kwiecinski/BMS-and-offgrid-photovoltaic-management-system/docs/energy-meters/gama350_diode_dimensions1.jpg

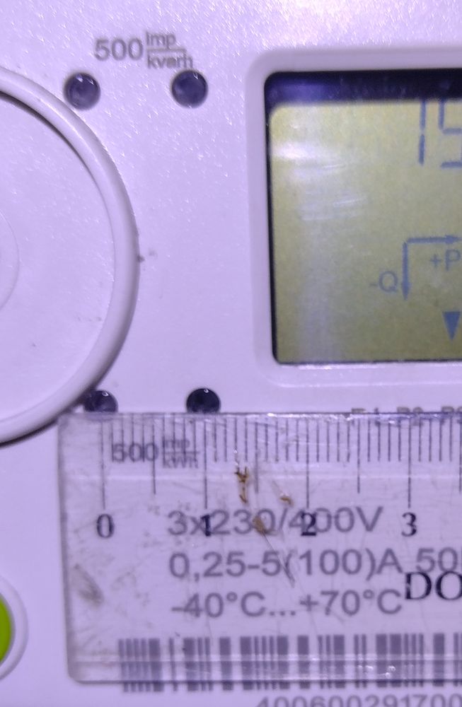
docs/energy-meters/gama350_diode_dimensions1.jpg
