kwiecinski/BMS-and-offgrid-photovoltaic-management-system/docs/FL-2C Shunt Resistor Dimensions.webp

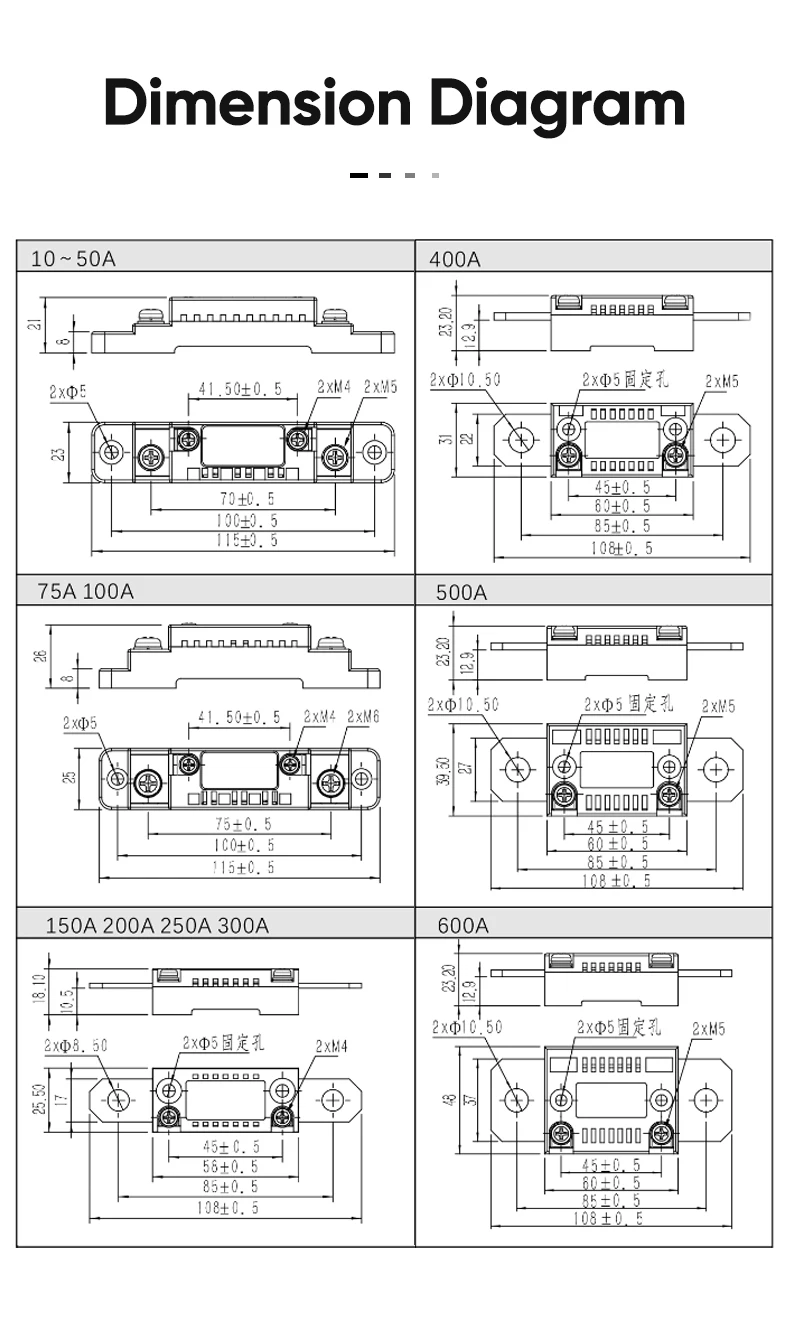
docs/FL-2C Shunt Resistor Dimensions.webp
