kwiecinski/BMS-and-offgrid-photovoltaic-management-system/docs/lt1492-voltage-controlled-current-sink.png

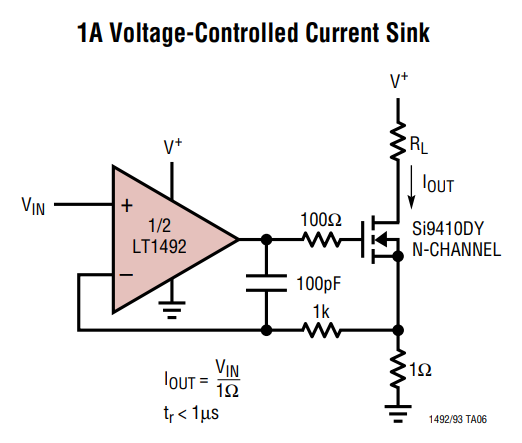
docs/lt1492-voltage-controlled-current-sink.png
