kwiecinski/BMS-and-offgrid-photovoltaic-management-system/docs/photos/ground-mount-structure/single_steel_post.jpg

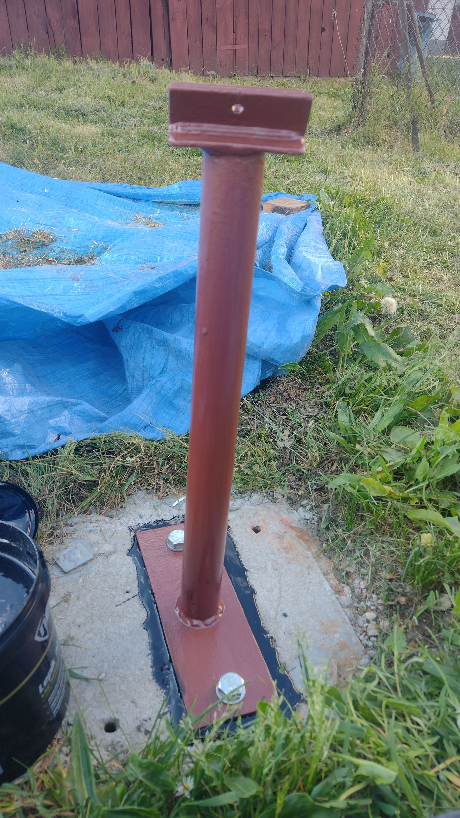
docs/photos/ground-mount-structure/single_steel_post.jpg
