kwiecinski/BMS-and-offgrid-photovoltaic-management-system/docs/photos/ground-mount-structure/steel-workshop-and-painting-09.jpg

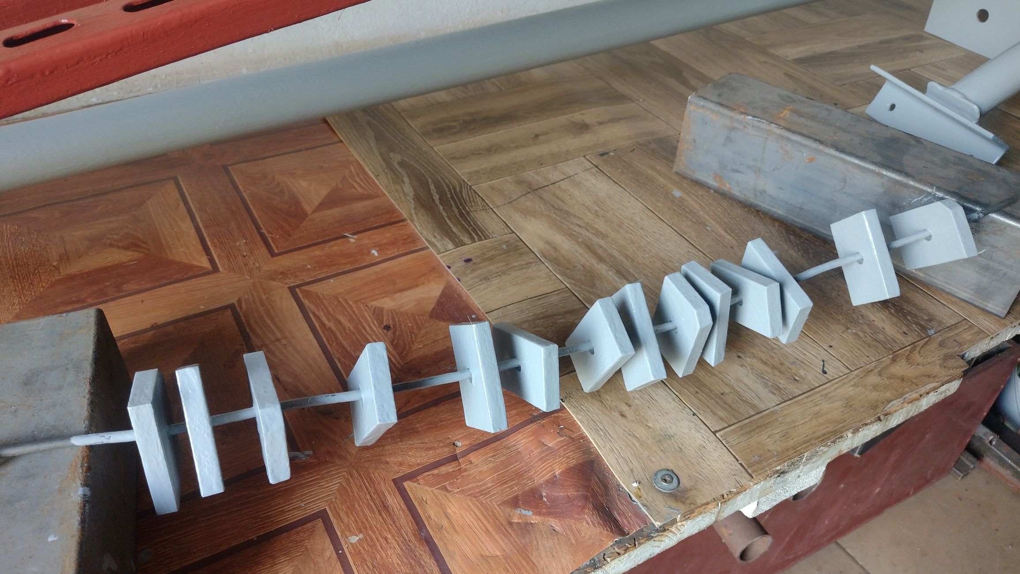
docs/photos/ground-mount-structure/steel-workshop-and-painting-09.jpg
