kwiecinski/BMS-and-offgrid-photovoltaic-management-system/docs/photos/shunt-resistor.jpg

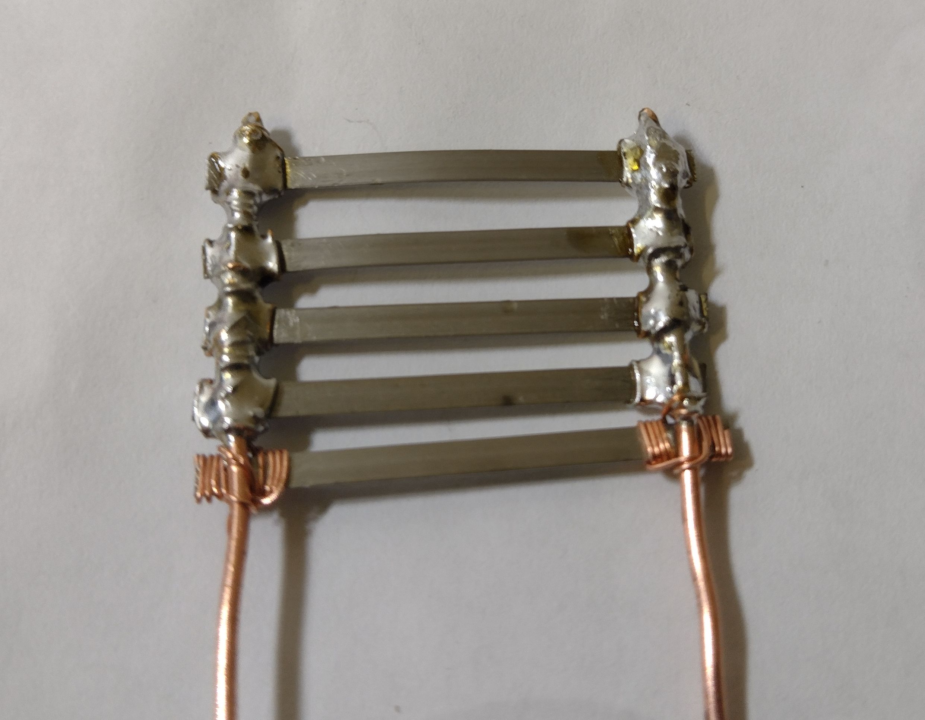
docs/photos/shunt-resistor.jpg
