kwiecinski/BMS-and-offgrid-photovoltaic-management-system/docs/xl4015/DC-DC-Buck-Converter.jpg

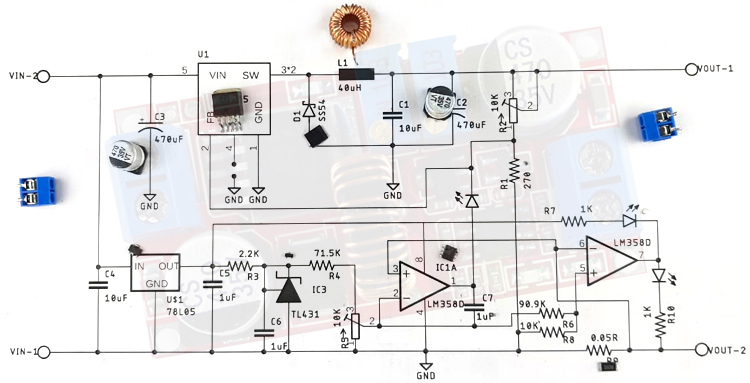
docs/xl4015/DC-DC-Buck-Converter.jpg
