kwiecinski/BMS-and-offgrid-photovoltaic-management-system/docs/zero crossing circuit.jpg

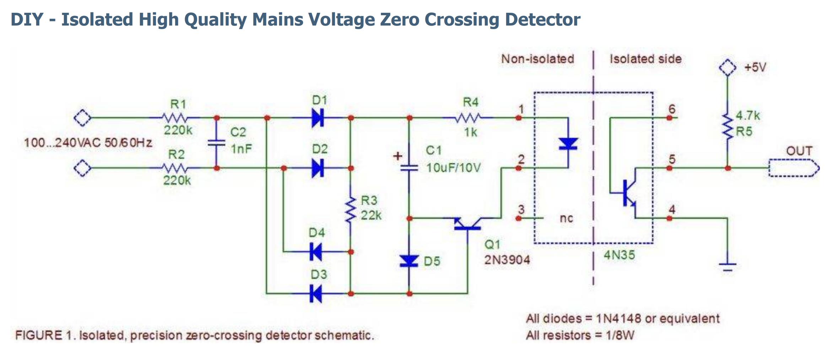
docs/zero crossing circuit.jpg
