kwiecinski/BMS-and-offgrid-photovoltaic-management-system/docs/connector/Phoenix contact SDDC 1,5 - 5-PV-3,5.pdf

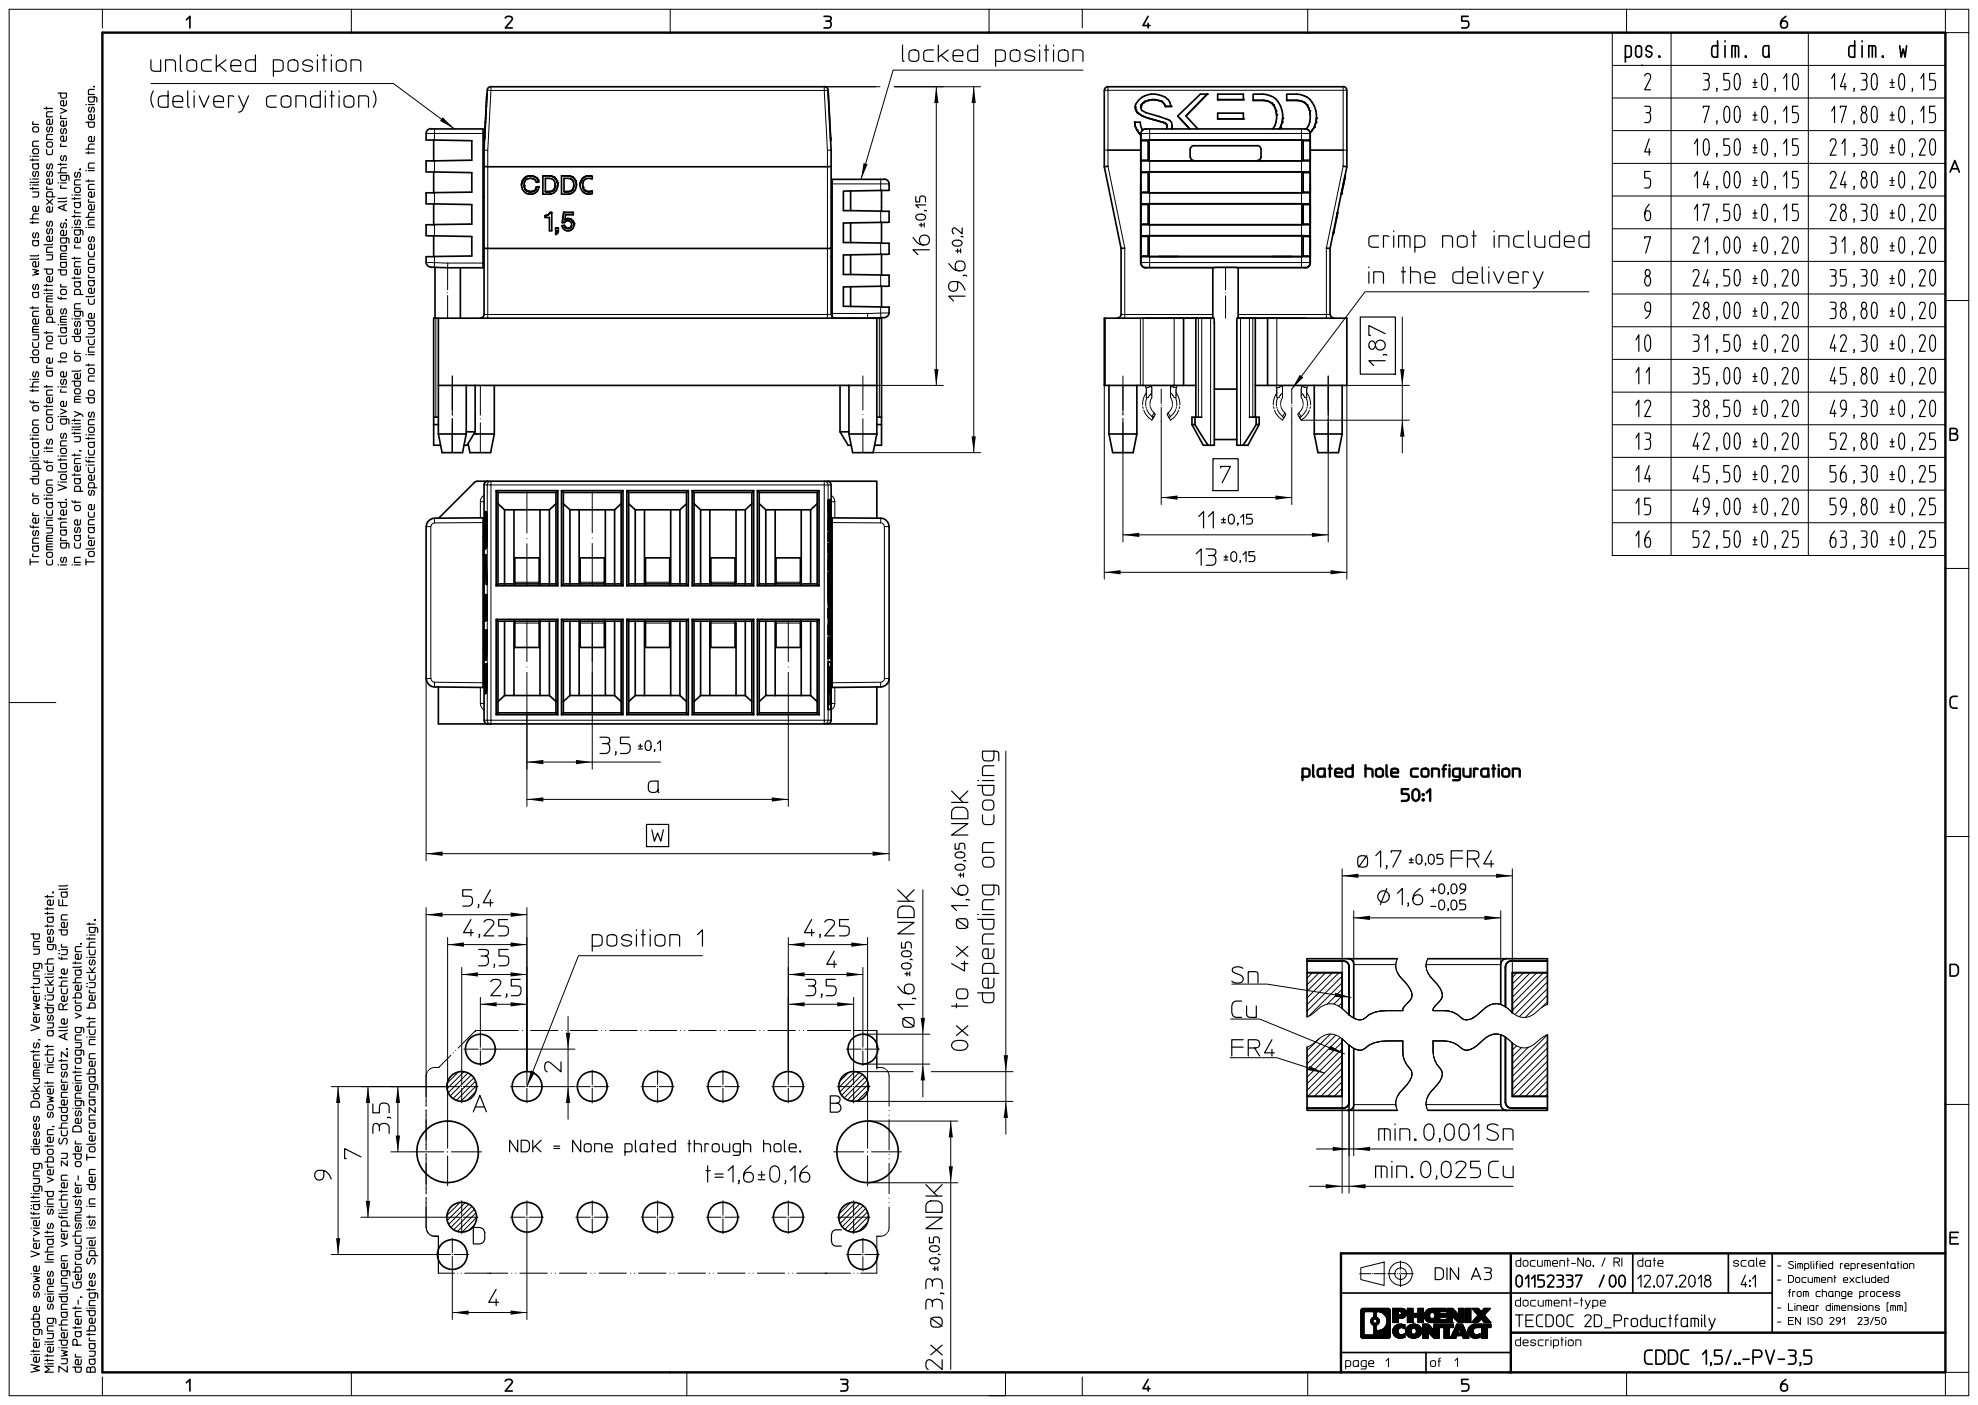
[picture p55: page 1]
