kwiecinski/BMS-and-offgrid-photovoltaic-management-system/simulation/analog_power_supply_op07.asc

C1: cap; 100p
C2: cap; 1000µ
C3: cap; 100p
D1: diode; 1N4148
D2: diode; 1N4148
Q1: npn; BC817-40
Q2: pnp; 2SA2094
Q3: pnp; D45H11
R1: res; 3k
R2: res; 10R
R3: res; 9k
R4: res; 1k
R5: res; 3k
R6: res; 1
R7: res; 1
R8: res; 10k
R9: res; 470
R11: res; 1k
U2: OP07
U3: OP07
V1: voltage; 12
V2: voltage; 5
V3: voltage; 5
V4: voltage; 50
V5: voltage; 5
V6: voltage; 5
Named nets: 0, -5V, +12v, +12V, +5V, Vout, base1
.tran 0 50m 100u
.include tl071.sub
