kwiecinski/BMS-and-offgrid-photovoltaic-management-system/simulation/analog_power_supply.asc

C1: cap; 1p
C2: cap; 100µ
C3: cap; 10n
D1: diode; 1N4148
D2: diode; 1N4148
D3: diode; 1N4148
D4: diode; 1N4148
Q1: pnp; BC807-25
Q2: npn; ZTX1048A
Q3: npn; ZTX1048A
Q4: npn; BC847A
R1: res; 100k
R2: res; 20R
R3: res; 9k
R4: res; 1k
R6: res; 1
R7: res; 1k
R8: res; 1
R9: res; 1k
R10: res; 1k
R12: res; 220R
U1: OP07
U2: OP07
V1: voltage; 12
V2: voltage; 5
V3: voltage; 5V
V4: voltage; 50
V5: voltage; 10
VREF: voltage; 2
Named nets: 0, -5V, +12v, Vout, +12V, +50V
.tran 0 50m 100n
.include tl071.sub
