kwiecinski/BMS-and-offgrid-photovoltaic-management-system/simulation/LTC4440.asc

C1: cap; 100n
C2: cap; 470µ
C3: cap; 1n
C4: cap; 10n
C5: cap; 100n
C6: cap; 10n
D1: schottky; 1N5819
D2: schottky; MBR745
D3: diode; 1N4148
D4: diode; 1N4148
D5: zener; BZX84C15L
L1: ind; 80µ
M1: nmos; BSC028N06LS3
R1: res; 10
R2: res; 10
R3: res; 100k
R4: res; 1k
U1: LTC4440
U2: NE555
V1: voltage; 12
V2: voltage; PULSE(0 5 0 1n 1n 1u 20u)
V3: voltage; 30
Named nets: 0, out, gate, source, neout
.tran 0 50m 0 1m
