kwiecinski/BMS-and-offgrid-photovoltaic-management-system/simulation/charge_pump_from_uc.asc

C1: cap; 10µ
C2: cap; 100µ
D1: diode; 1N4148
D2: diode; 1N4148
Q1: npn; BC817-25
Q2: npn; BC817-25
Q3: pnp; BC557C
R1: res; 10k
R2: res; 1k
R3: res; 200
V1: voltage; 5
V2: voltage; PULSE(0 5 1n 1n 1n 100u 200u)
Named nets: 0
.tran 0 100m 1m
