kwiecinski/BMS-and-offgrid-photovoltaic-management-system/simulation/gnd_diff.asc

R1: res; 10
R2: res; 1k
R3: res; 0.5
R4: res; 1Meg
R5: res; 0.5
R6: res; 0.1
R7: res; 10k
R8: res; 10k
R10: res; 10k
R11: res; 10k
R12: res; 1k
R13: res; 10k
R14: res; 10k
R15: res; 10k
R16: res; 10k
U1: ADTL082
U2: ADTL082
U3: ADTL082
V1: voltage; -5
V2: voltage; -10
V3: voltage; 12
V4: voltage; 30
V5: voltage; 2.5
V6: voltage; 500m
Named nets: 0, out, gnd_clean, vref, +12V, vbat
.tran 0 3m 0 200n
