kwiecinski/BMS-and-offgrid-photovoltaic-management-system/simulation/gnd_diff_opamp_tl082.asc

R1: res; 10
R2: res; 1k
R3: res; 0.5
R4: res; 1Meg
R5: res; 0.5
R6: res; 0.1
R7: res; 100k
R8: res; 10k
R9: res; 100k
R10: res; 100k
R11: res; 47k
R12: res; 47k
U1: ADTL082
U2: ADTL082
V1: voltage; -5
V2: voltage; -10
V3: voltage; 6.5
V4: voltage; 30
V5: voltage; 2.5
Named nets: 0, out, gnd_clean, +12V, vbat, vref
.tran 0 10m 0 100u
