kwiecinski/BMS-and-offgrid-photovoltaic-management-system/simulation/totem-pole driver low side.asc

M1: nmos; BSB015N04NX3
Q1: npn; BC337-40
Q2: pnp; BC327-40
Q3: npn; BC847B
R1: res; 10
R2: res; 5
R4: res; 5k
R5: res; 5k
R6: res; 220
V1: voltage; 10
V2: voltage; PULSE(0 5 1n 1n 1n 10u 50u)
V3: voltage; 10
Named nets: 0, pulse_source, out, gate
.tran 0 200u 0 10n startup
