kwiecinski/BMS-and-offgrid-photovoltaic-management-system/simulation/driver_chip.asc

M1: nmos; BSB015N04NX3
Q1: npn
R1: res; 1k
R2: res; 5
R4: res; 1k
U1: ADP3654
V1: voltage; 30
V2: voltage; PULSE(0 5 1n 1n 1n 1u 10u)
V3: voltage; 15
Named nets: 0, pulse_source, gate
.tran 0 80u 0 5n startup
