kwiecinski/BMS-and-offgrid-photovoltaic-management-system/simulation/totem-pole driver low side complementary.asc

C1: cap; 220p
M1: nmos; BSB015N04NX3
Q1: npn; BC337-40
Q2: pnp; BC327-40
Q3: npn; BC847B
Q4: pnp; BC327-40
Q5: pnp; BC327-40
Q6: npn; BC337-40
Q7: npn; BC847B
R1: res; 10
R2: res; 5
R3: res; 1k
R4: res; 470
R5: res; 10k
R6: res; 680
R7: res; 220
R8: res; 330
R9: res; 330
R10: res; 330
R11: res; 10k
R12: res; 470
R13: res; 470
V1: voltage; 12
V2: voltage; PULSE(0 5 1n 1n 1n 500n 40u)
Named nets: 0, pulse_source, out, gate
.tran 0 200u 0 10n startup
