kwiecinski/BMS-and-offgrid-photovoltaic-management-system/simulation/pnp_driver.asc

D2: schottky; 1N5819
Q1: pnp; 2SB1705
Q2: pnp; 2SB1705
Q3: npn; BC847B
R1: res; 1k
R2: res; 5
R3: res; 1k
R4: res; 4k7
V1: voltage; 28
V2: voltage; PULSE(0 5 1n 1n 1n 1u 50u)
V3: voltage; 14
Named nets: 0, pulse_source
.tran 0 200u 0 10n startup
