kwiecinski/BMS-and-offgrid-photovoltaic-management-system/simulation/totem-pole driver.asc

C1: cap; 10n
C2: cap; 10n
D1: schottky; BAT54
D2: schottky; 1N5819
M1: nmos; BSB015N04NX3
Q1: npn; BC337-40
Q2: pnp; BC327-40
Q3: npn; BC847B
R1: res; 100
R2: res; 5
R3: res; 0
R4: res; 4k7
R5: res; 1.5k
R7: res; 100
V1: voltage; 28
V2: voltage; PULSE(0 5 1n 1n 1n 5u 50u)
V3: voltage; 14
Named nets: 0, pulse_source, out, gate
.tran 0 200u 0 10n startup
