kwiecinski/BMS-and-offgrid-photovoltaic-management-system/simulation/tl494_buck.asc

C1: cap; 2.2n
C2: cap; 2000µ
C3: cap; 100n
D1: diode; 1N4148
D2: schottky; RB215T-90NZ
D3: diode; 1N4148
L1: ind; 38µ
M1: nmos; IRF7468
Q1: npn; BC337-40
Q2: pnp; BC327-40
Q3: npn; BC337-40
R1: res; 1K; tol=1 pwr=0.1
R2: res; 100; tol=1 pwr=0.1
R3: res; 5k
R4: res; 1k
R5: res; 10
R6: res; 300m
R7: res; 6.8k
R8: res; 4.7k
R9: res; 10k
R10: res; 51k
R11: res; 510
R12: res; 10k
R13: res; 100
R14: res; 1K; tol=1 pwr=0.1
U2: TL494
V1: voltage; 27
Named nets: 0, out, emiter_drive, gate
.tran 0 5m 0 1m uic
