kwiecinski/BMS-and-offgrid-photovoltaic-management-system/simulation/high_side_current_sense.asc

Q1: npn; BC817-40
R1: res; 6
R2: res; 10m
R3: res; 1k
R4: res; 100R
R5: res; 1k
R6: res; 10R
U2: ADTL082
V1: voltage; 28
V2: voltage; 31
Named nets: 0, diff_out
.tran 0 50m 0 5u
