kwiecinski/BMS-and-offgrid-photovoltaic-management-system/simulation/diff_opamp.asc

C1: cap; 10µ
C2: cap; 47µ
C4: cap; 47µ
D1: diode; 1N4148
D2: diode; 1N4148
D4: diode; 1N4148
D5: zener; UDZV30B
D6: diode; 1N4148
L1: ind; 47µ
M1: nmos
Q1: npn; BC547C
Q2: npn; BC547C
Q3: pnp; BC557C
Q4: npn; BC547C
Q5: pnp; BC557C
Q6: npn; BC547C
Q7: npn; BC547C
R1: res; 100; tol=5
R2: res; 102; tol=5
R3: res; 100
R4: res; 1k
R5: res; 0.1
R6: res; 10
R7: res; 1k
R9: res; 1k
R10: res; 10k
R11: res; 1k
U1: ADTL082
V1: voltage; 32
V2: voltage; 29
V4: voltage; PULSE(0 5 0 0 0 50u 100u)
V5: voltage; 5
Named nets: 0, out, vopamp, -V
.tran 0 25m 0 200n
