kwiecinski/BMS-and-offgrid-photovoltaic-management-system/simulation/fan_reg.asc

C1: cap; 1µ
C2: cap; 470µ
Q1: npn; 2SC5866
R1: res; 2k2
R2: res; 100k
R3: res; 1k
R4: res; 10k
R5: res; 6.2k
R6: res; 24
U1: LM358
V1: voltage; 13.8
V2: voltage; PULSE(0 5 1n 1n 1n  {Tperiod-Ton} {Tperiod})
V3: voltage; 28
Named nets: 0, out, base, pwm_filtered
.tran 0 15m 0 500n
.param duty=0
.param freq=10k
.param Tperiod={1/freq}
.param Ton={Tperiod*duty}
