kwiecinski/BMS-and-offgrid-photovoltaic-management-system/simulation/fan_smps.asc

C1: cap; 470µ
C2: cap; 22n
D1: schottky; RBR30NS40A
D2: diode; 1N4148
D3: diode; 1N4148
L1: ind; 35µ
M1: nmos; IRFH5406
Q1: npn; BC337-40
Q2: pnp; BC327-40
Q3: npn; BC847B
R1: res; 5R
R2: res; 100R
R3: res; 4k7
R4: res; 4k7
V1: voltage; 28
V2: voltage; PULSE(0 5 1n 1n 1n 5u 10u)
V3: voltage; -12
Named nets: 0, OUT, pulse_source, gate, source
.tran 0 5m 0 50n startup
