kwiecinski/BMS-and-offgrid-photovoltaic-management-system/electrical/PV_electrical.kicad_sch

## KiCad design electrical/PV_electrical.kicad_sch (2025-04-28)

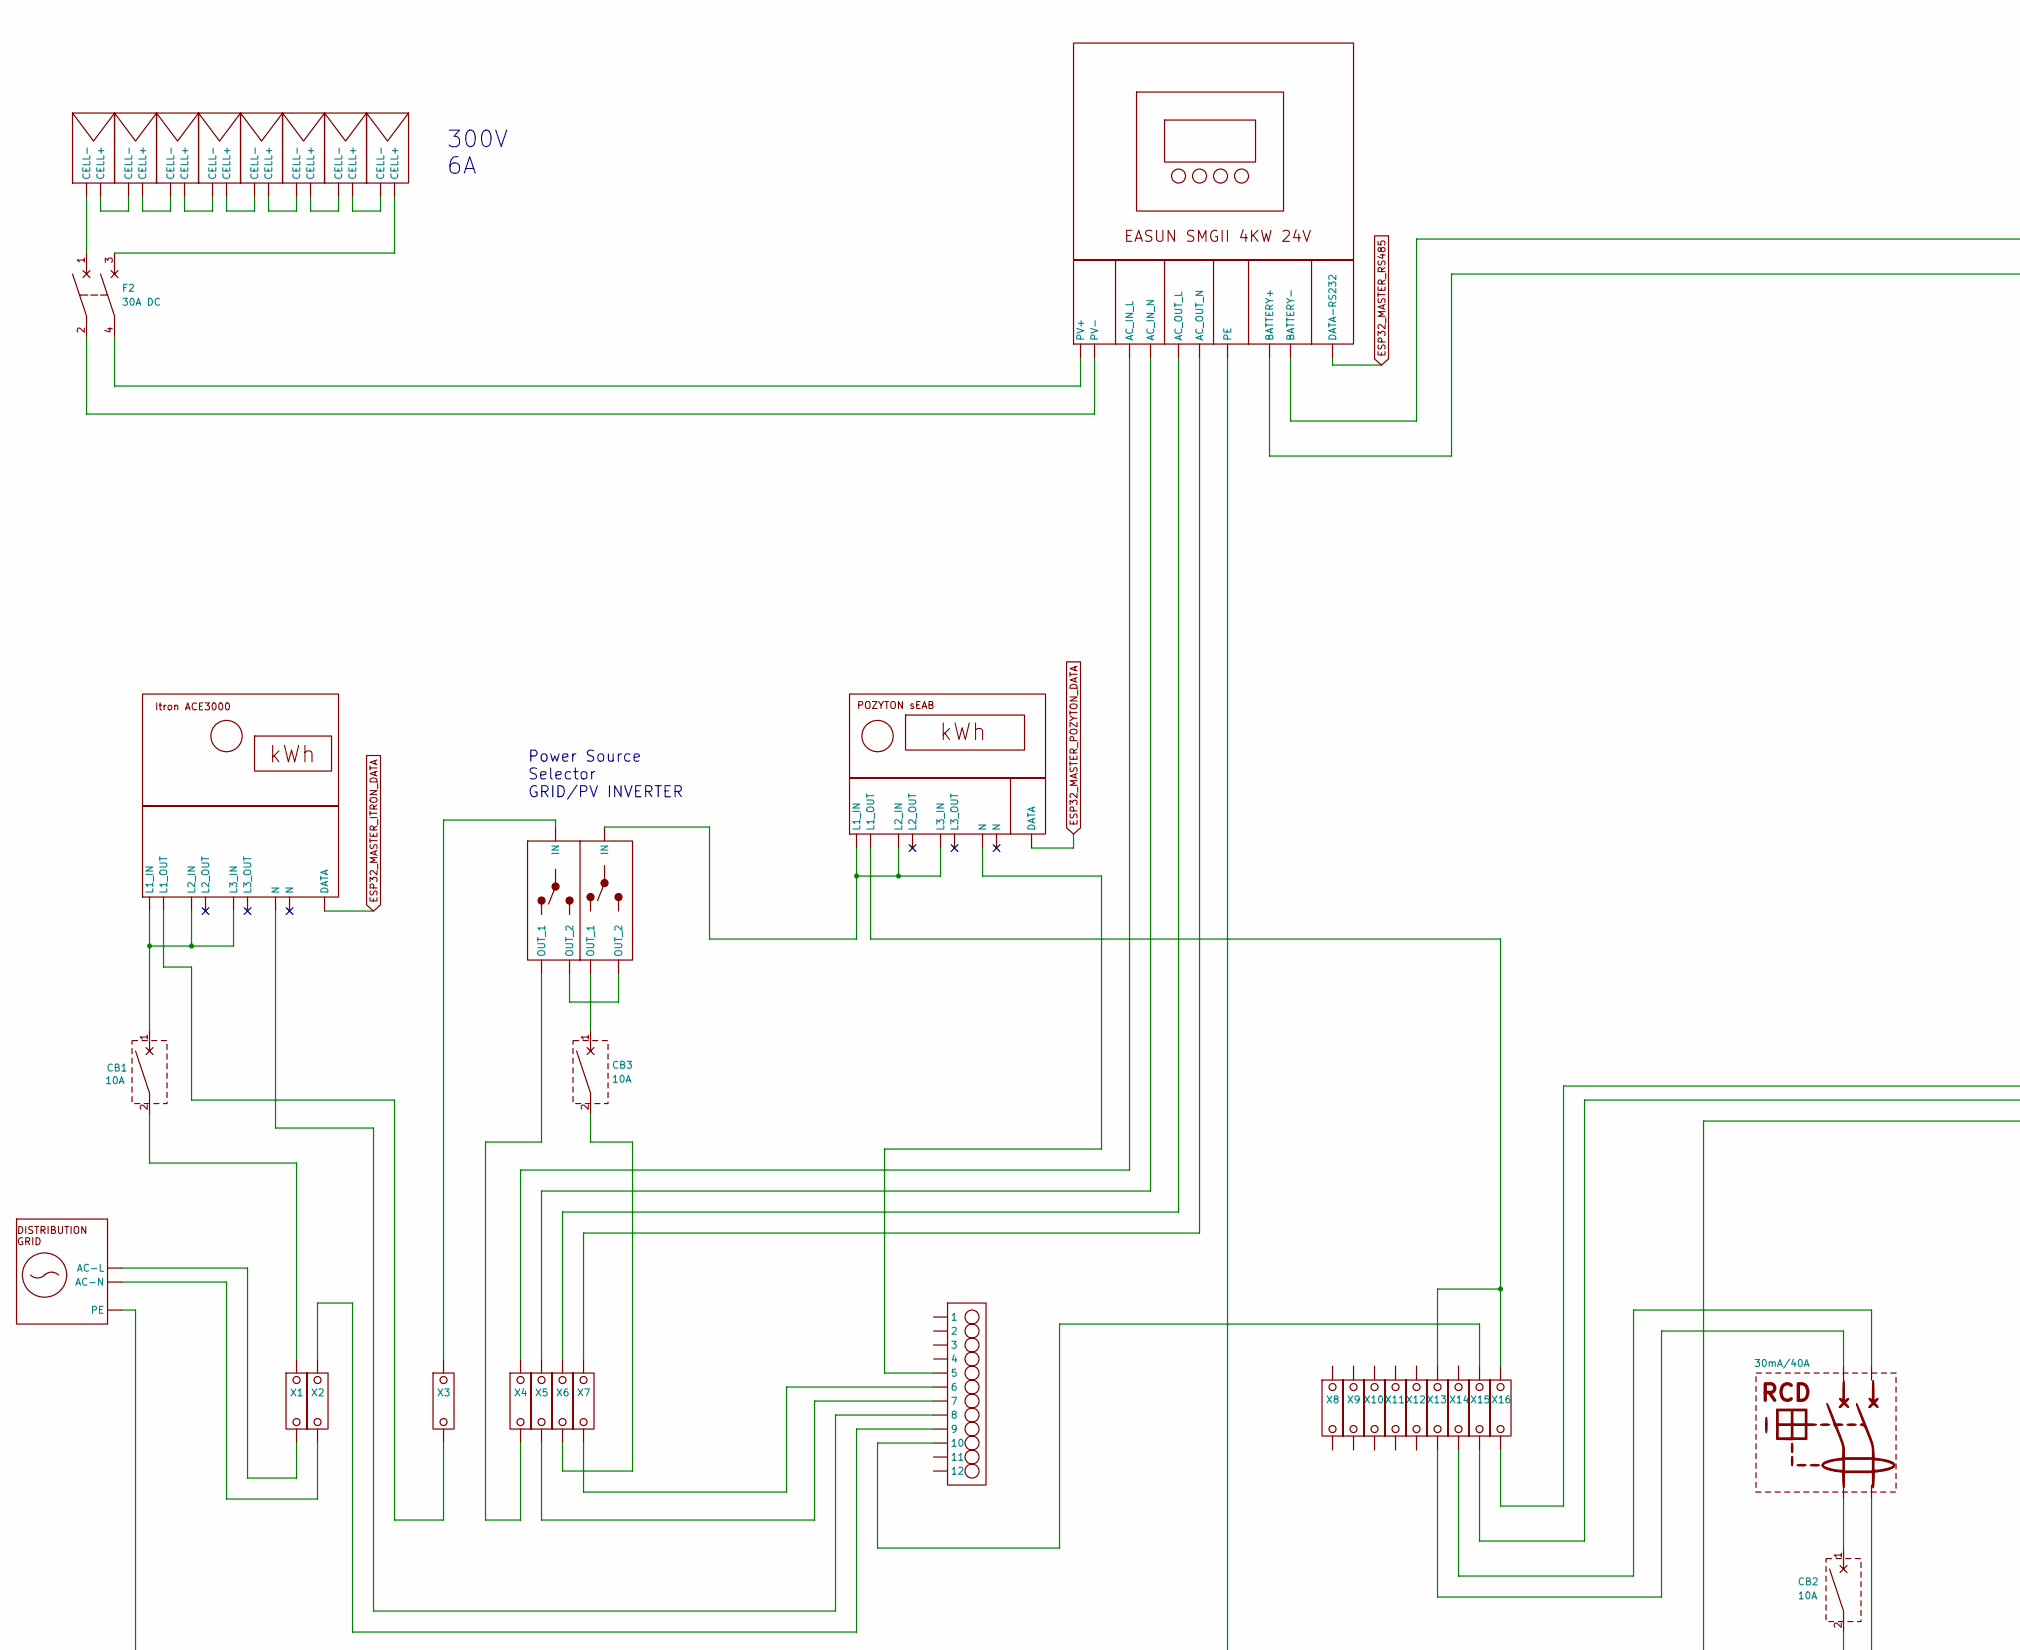
[picture p103: schematic PV_electrical.kicad_sch, part in row 1, column 1]

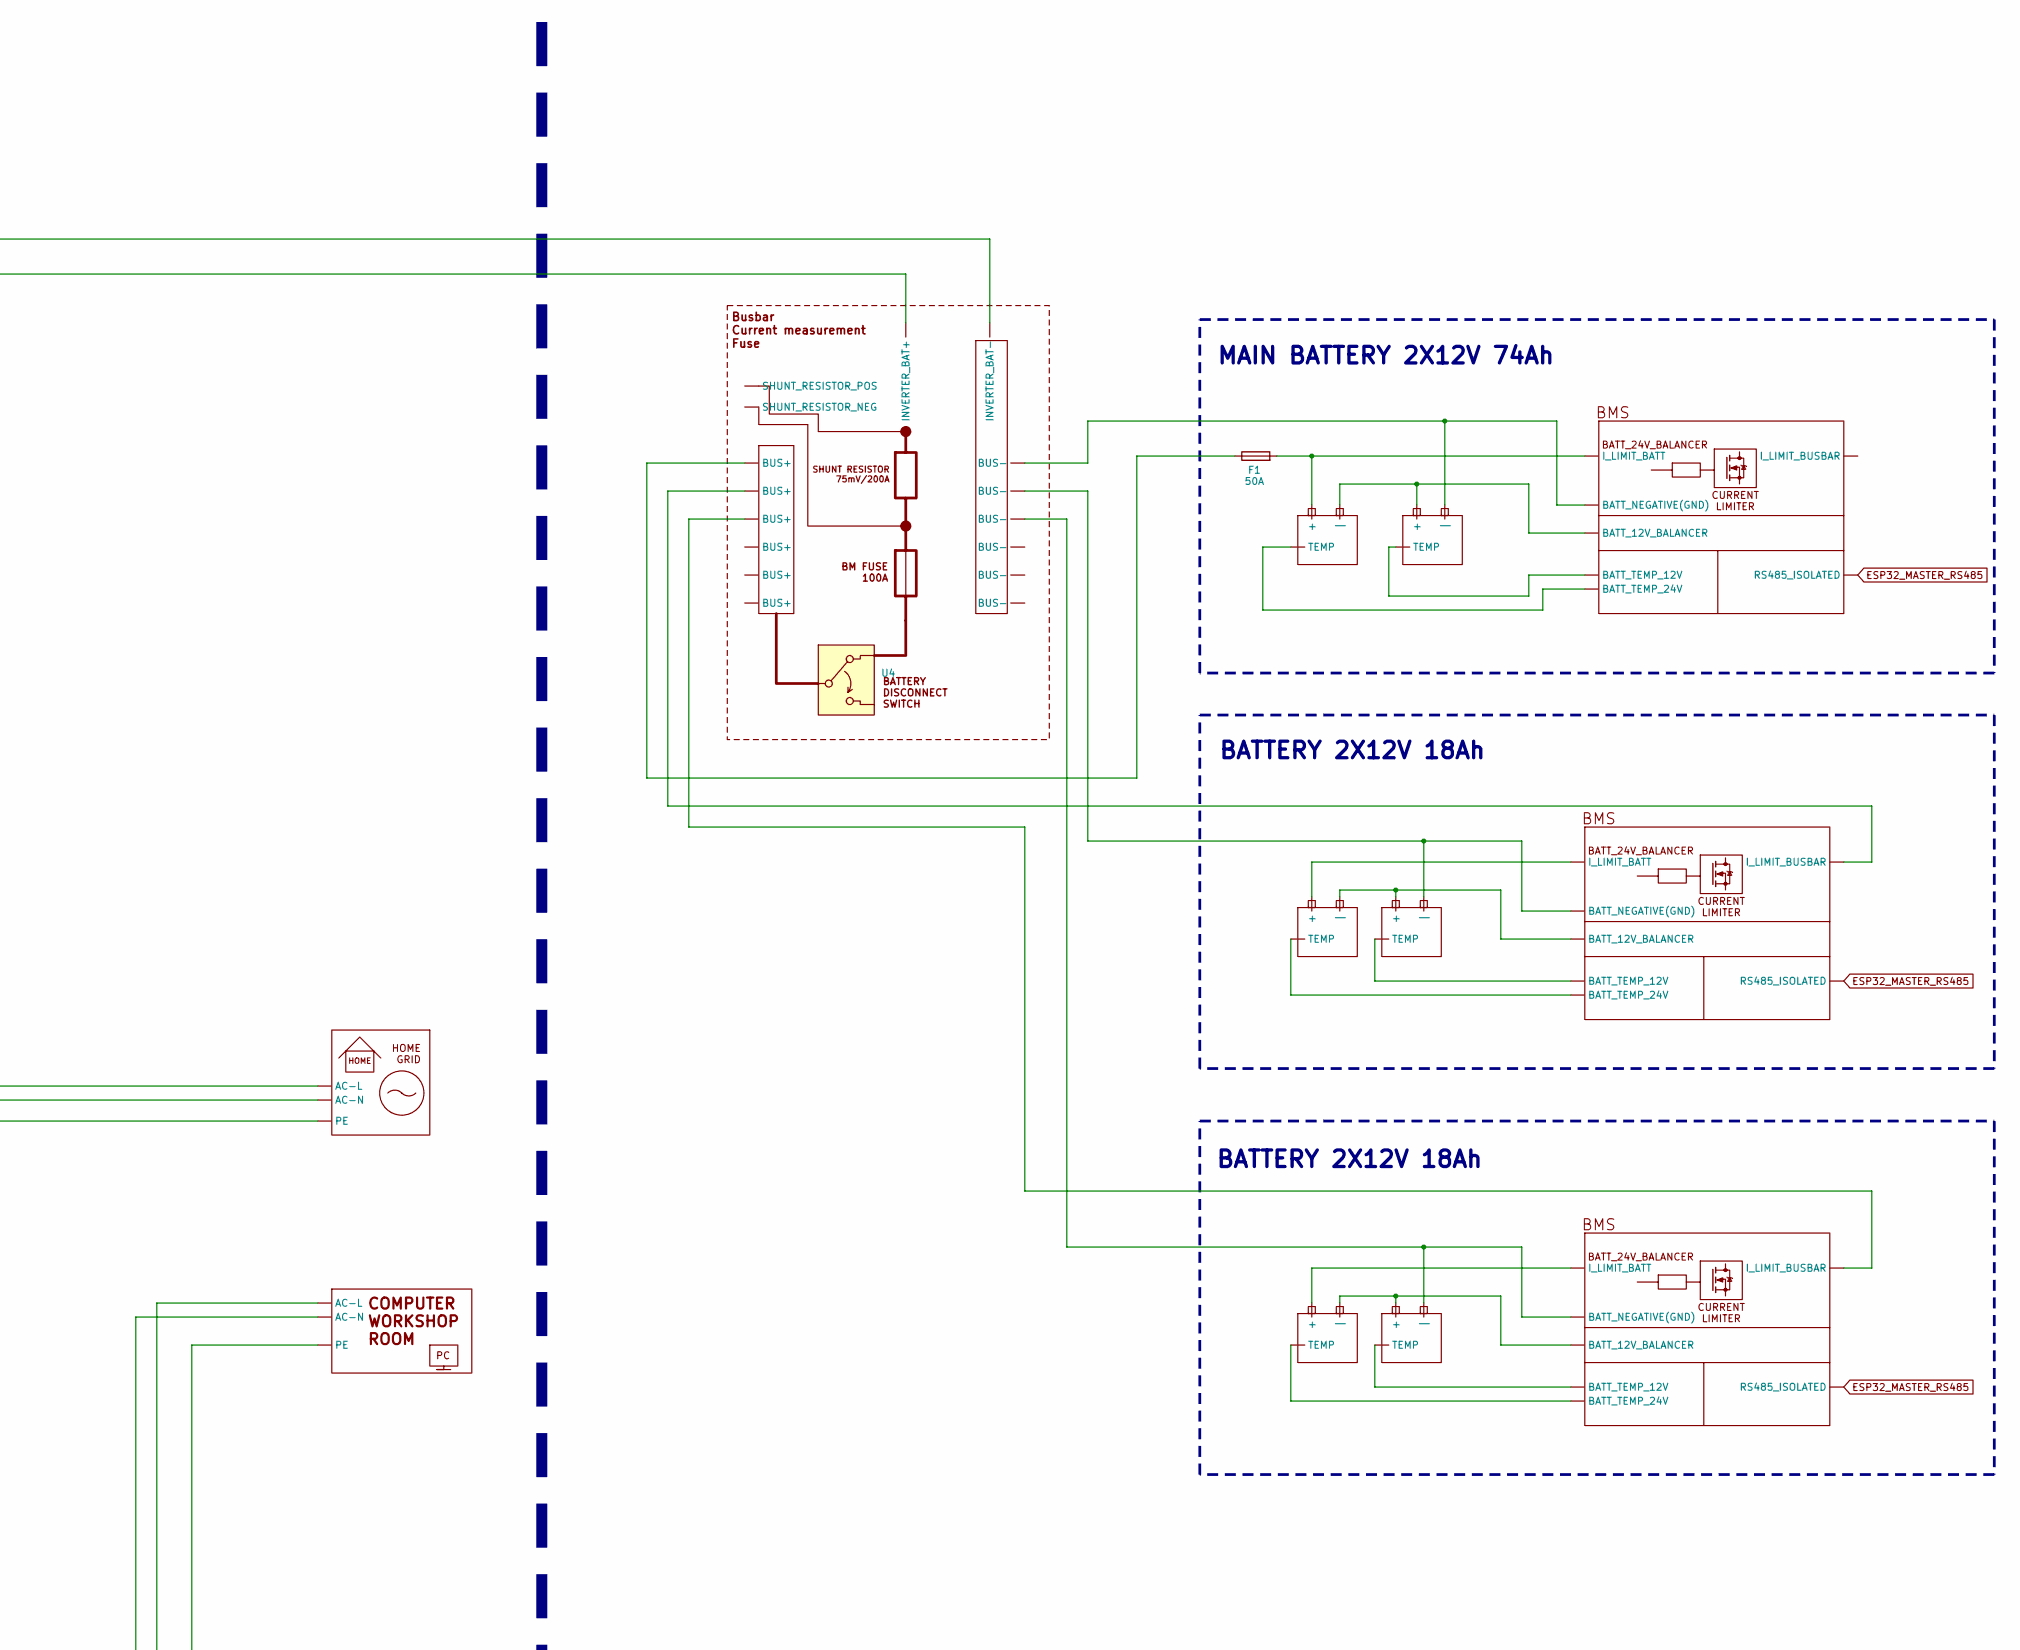
[picture p104: schematic PV_electrical.kicad_sch, part in row 1, column 2]

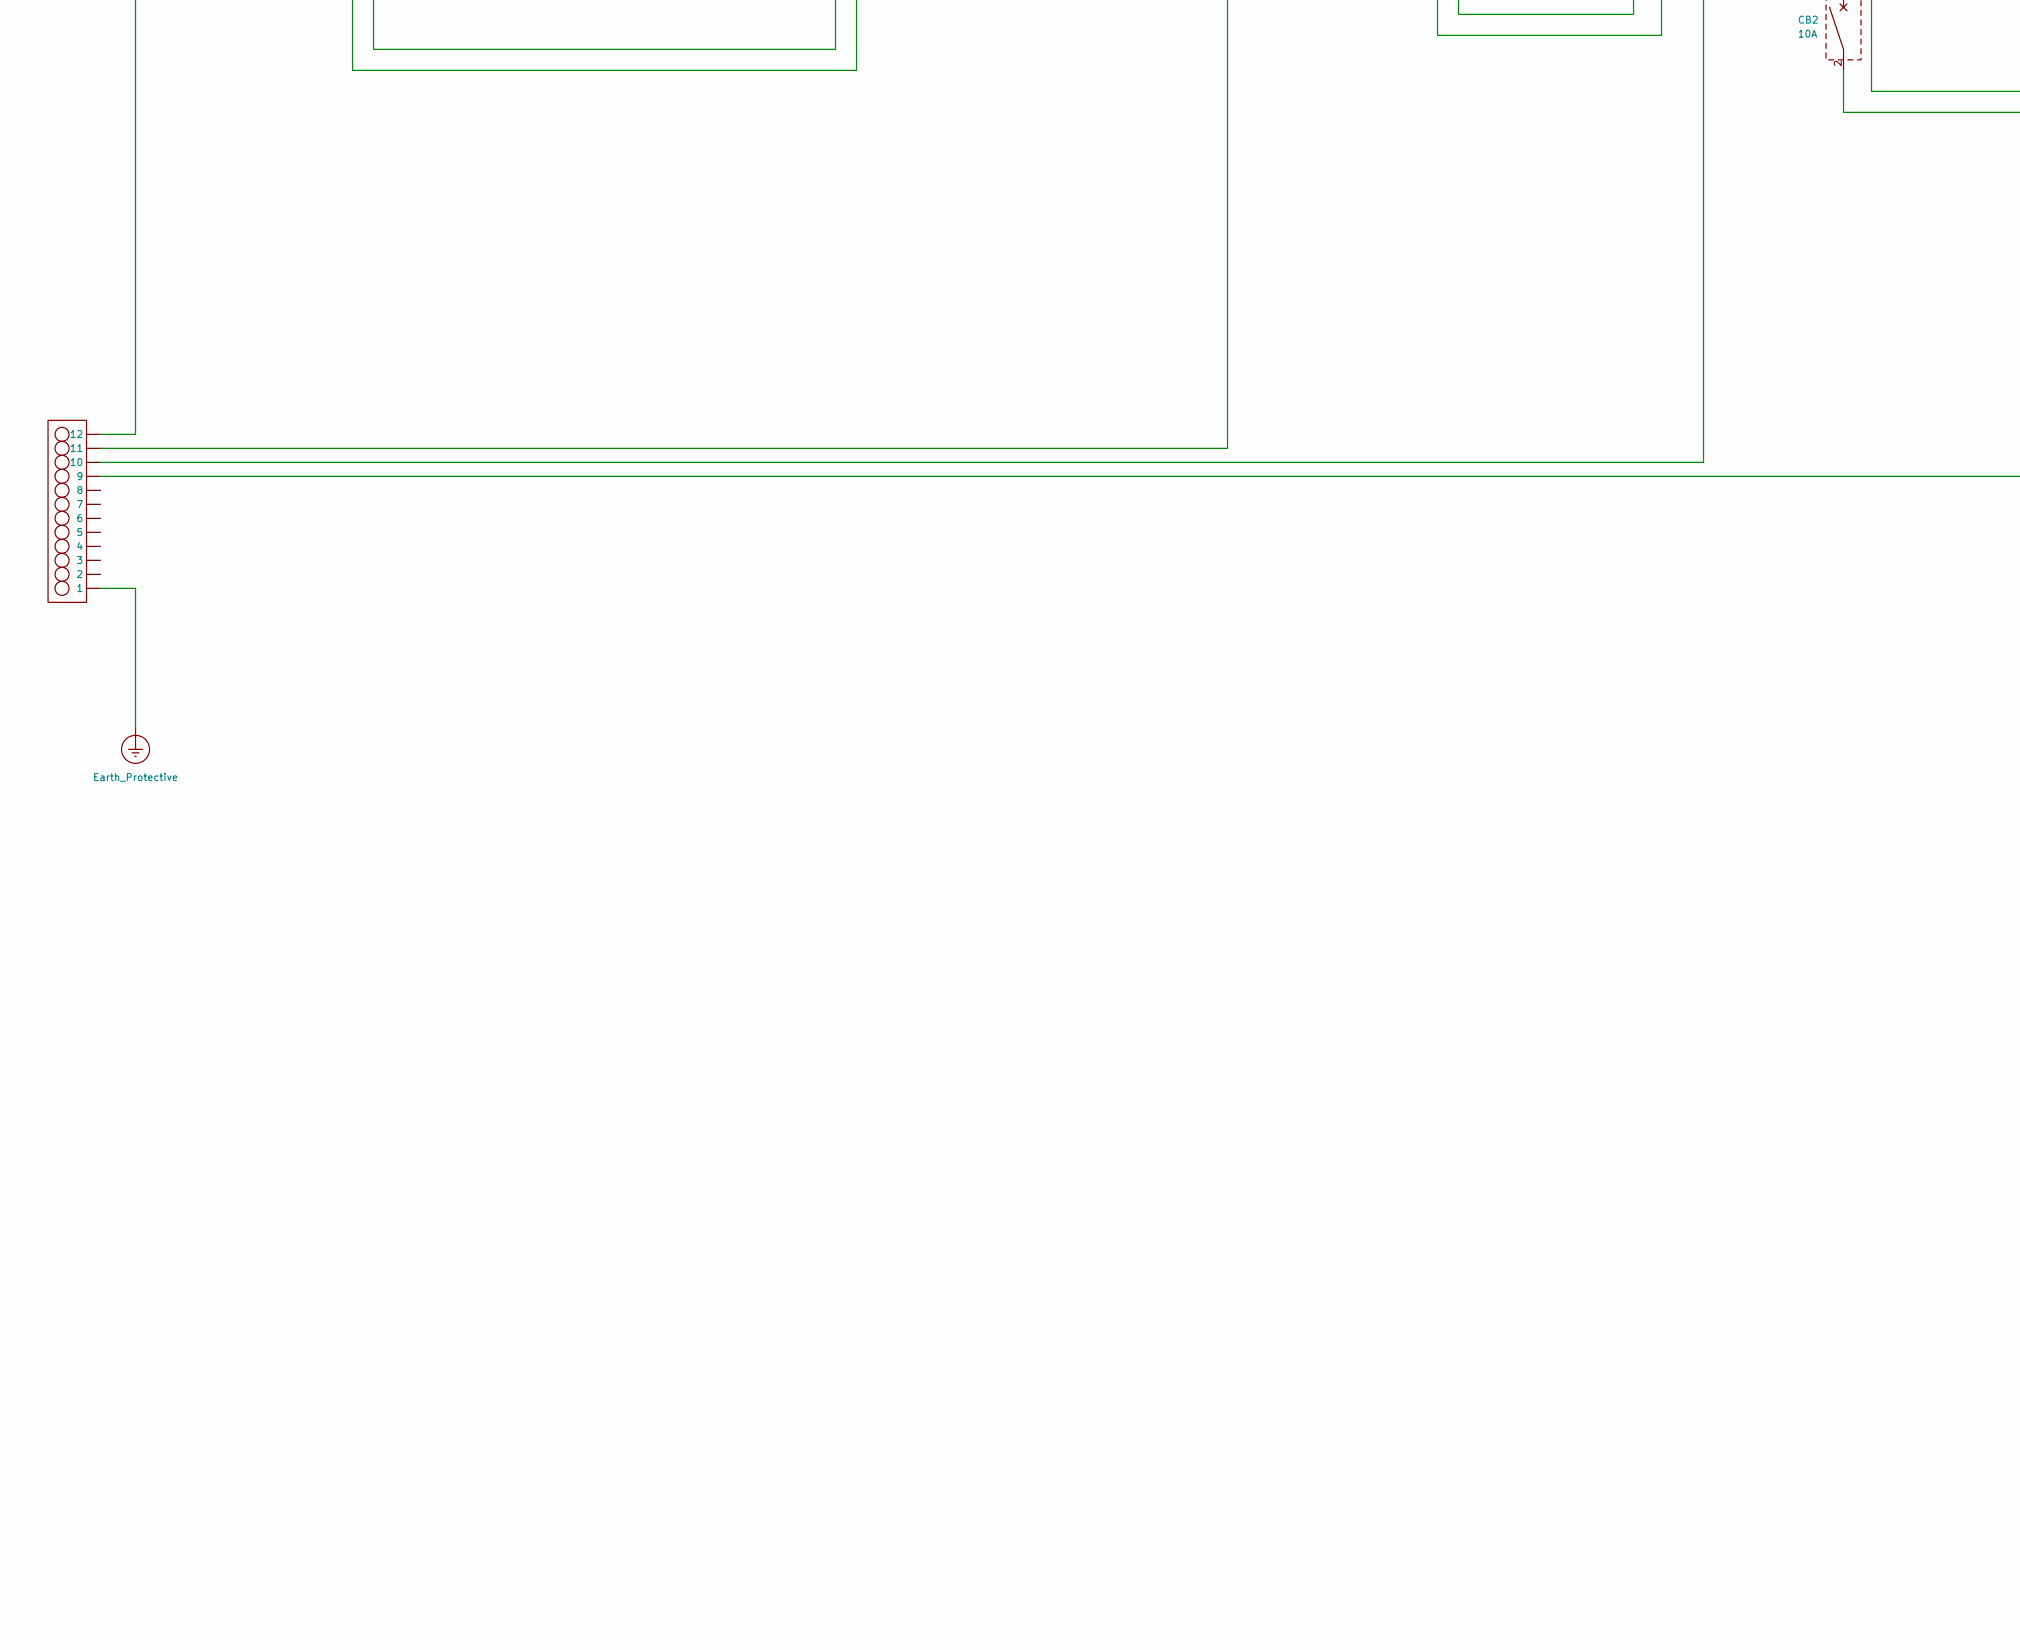
[picture p105: schematic PV_electrical.kicad_sch, part in row 2, column 1]

Parts:
B1, B2, B3, B4, B5, B6, B7, B8: (no value)
BAT1, BAT2, BAT3, BAT4, BAT5, BAT6: (no value)
BMS1, BMS2, BMS3: (no value)
CB1, CB2, CB3: 10A
D1: (no value)
F1: 50A
F2: 30A DC
F3: 30mA/40A
J1, J2: (no value)
M1: Itron ACE3000
M2: Pozyton-sEAB
SW1: (no value)
U1, U2, U3, U4: (no value)
X1, X2, X3, X4, X5, X6, X7, X8, X9, X10, X11, X12, X13, X14, X15, X16: (no value)

Connections:
ESP32_MASTER_ITRON_DATA: M1.
ESP32_MASTER_POZYTON_DATA: M2.
ESP32_MASTER_RS485: BMS1., BMS2., BMS3., U2.
Earth_Protective: J1.
unnamed: B1., B2., F2.1
unnamed: B2., B3.
unnamed: B3., B4.
unnamed: B4., B5.
unnamed: B5., B6.
unnamed: B6., B7.
unnamed: B7., B8.
unnamed: B8., F2.3
unnamed: BAT1., BAT2., BMS1., F1.2
unnamed: BAT2., BMS1., U4.
unnamed: BAT3., BAT4., BMS2.
unnamed: BAT4., BMS2., U4.
unnamed: BAT5., BAT6., BMS3.
unnamed: BAT6., BMS3., U4.
unnamed: BMS2., U4.
unnamed: BMS3., U4.
unnamed: CB1.1, M1.
unnamed: CB1.2, X1.
unnamed: CB2.1, F3.
unnamed: CB2.2, D1.
unnamed: CB3.1, SW1.
unnamed: CB3.2, X6.
unnamed: D1., F3., J1.
unnamed: F1.1, U4.
unnamed: F2.2, U2.
unnamed: F2.4, U2.
unnamed: F3., X13., X14.
unnamed: J1., U1., U2., U3.
unnamed: J2., M1., M2., X2., X5., X7., X15.
unnamed: M1., X3.
unnamed: M2., SW1., X13., X16.
unnamed: SW1., X3., X4.
unnamed: U1., X1., X2.
unnamed: U2., U4., X4., X5., X6., X7.
unnamed: U3., X15., X16.

Notes on the sheet:
Power Source Selector GRID/PV INVERTER
BATTERY 2X12V 18Ah
MAIN BATTERY 2X12V 74Ah
300V 6A
