kwiecinski/BMS-and-offgrid-photovoltaic-management-system/hardware/PCB_and_schematic/MPPT_controller/ESP_32_energy_meters_probe.kicad_sch

## KiCad design hardware/PCB_and_schematic/MPPT_controller/ESP_32_energy_meters_probe.kicad_sch (2024-09-15)

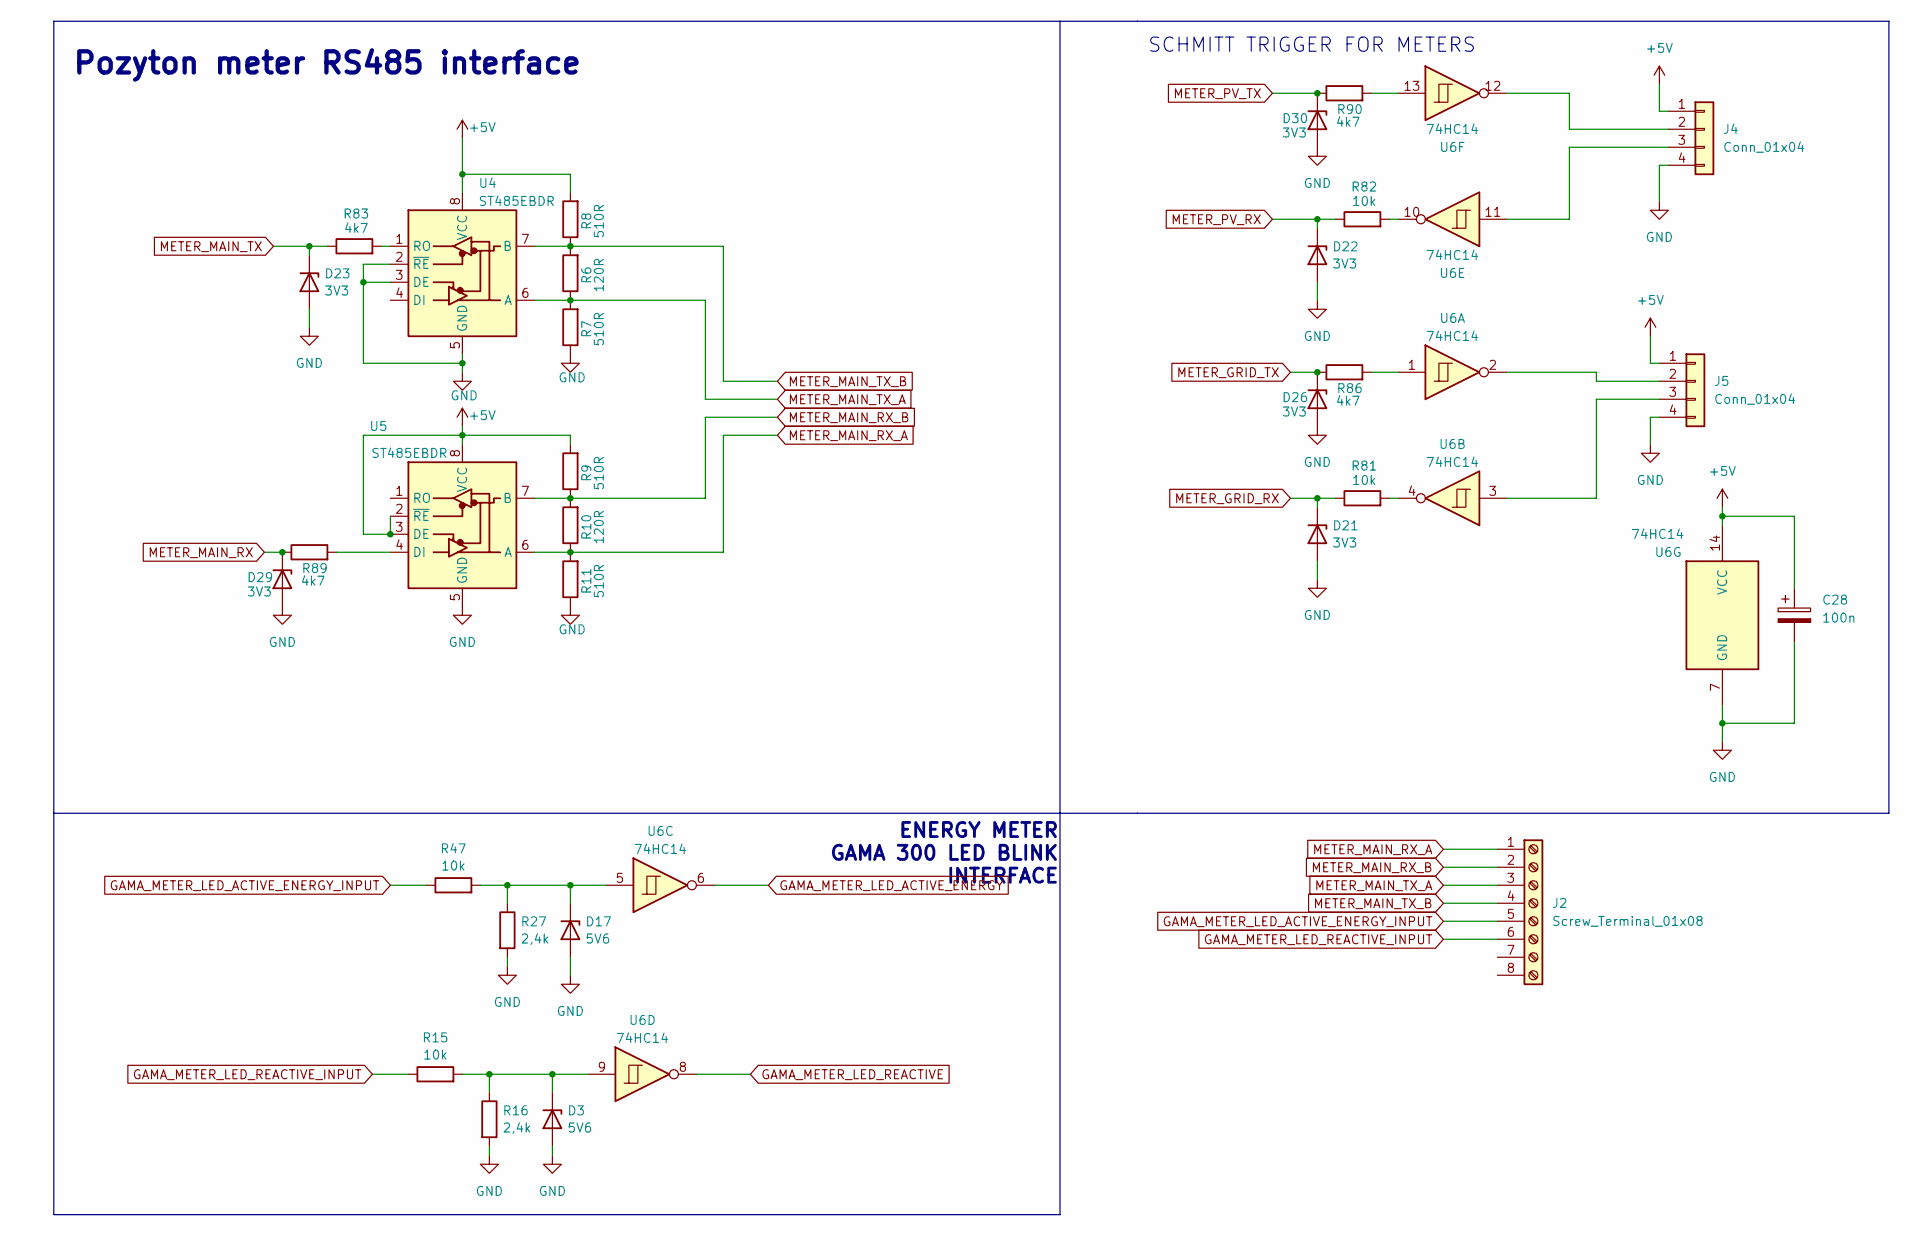
[picture p106: schematic ESP_32_energy_meters_probe.kicad_sch]

Parts:
C28: 100n; C_0805_2012Metric
D3, D17: 5V6; D_MiniMELF
D21, D22, D23, D26, D29, D30: 3V3; D_MiniMELF
J2: Screw_Terminal_01x08; TerminalBlock_bornier-8_P5.08mm
J4, J5: Conn_01x04; JST_EH_B4B-EH-A_1x04_P2.50mm_Vertical
R6, R10: 120R; R_0805_2012Metric_Pad1.20x1.40mm_HandSolder
R7, R8, R9, R11: 510R; R_0805_2012Metric_Pad1.20x1.40mm_HandSolder
R15, R47, R81, R82: 10k; R_0805_2012Metric_Pad1.20x1.40mm_HandSolder
R16, R27: 2,4k; R_0805_2012Metric_Pad1.20x1.40mm_HandSolder
R83, R86, R89, R90: 4k7; R_0805_2012Metric_Pad1.20x1.40mm_HandSolder
U4, U5: ST485EBDR; SOIC-8_3.9x4.9mm_P1.27mm
U6: 74HC14; SOIC-14_3.9x8.7mm_P1.27mm

Connections:
+5V: C28.1, J4.1, J5.1, R8.2, R9.2, U4.8 (VCC), U5.2 (~RE), U5.3 (DE), U5.8 (VCC), U6.14 (VCC)
GAMA_METER_LED_ACTIVE_ENERGY: U6.6
GAMA_METER_LED_ACTIVE_ENERGY_INPUT: J2.5, R47.1
GAMA_METER_LED_REACTIVE: U6.8
GAMA_METER_LED_REACTIVE_INPUT: J2.6, R15.1
GND: C28.2, D3.2 (A), D17.2 (A), D21.2 (A), D22.2 (A), D23.2 (A), D26.2 (A), D29.2 (A), D30.2 (A), J4.4, J5.4, R7.1, R11.1, R16.2, R27.2, U4.2 (~RE), U4.3 (DE), U4.5 (GND), U5.5 (GND), U6.7 (GND)
METER_GRID_RX: D21.1 (K), R81.1
METER_GRID_TX: D26.1 (K), R86.1
METER_MAIN_RX: D29.1 (K), R89.1
METER_MAIN_RX_A: J2.1, R10.1, R11.2, U5.6 (A)
METER_MAIN_RX_B: J2.2, R9.1, R10.2, U5.7 (B)
METER_MAIN_TX: D23.1 (K), R83.1
METER_MAIN_TX_A: J2.3, R6.1, R7.2, U4.6 (A)
METER_MAIN_TX_B: J2.4, R6.2, R8.1, U4.7 (B)
METER_PV_RX: D22.1 (K), R82.1
METER_PV_TX: D30.1 (K), R90.1
unnamed: D3.1 (K), R15.2, R16.1, U6.9
unnamed: D17.1 (K), R27.1, R47.2, U6.5
unnamed: J4.2, U6.12
unnamed: J4.3, U6.11
unnamed: J5.2, U6.2
unnamed: J5.3, U6.3
unnamed: R81.2, U6.4
unnamed: R82.2, U6.10
unnamed: R83.2, U4.1 (RO)
unnamed: R86.2, U6.1
unnamed: R89.2, U5.4 (DI)
unnamed: R90.2, U6.13

Notes on the sheet:
Pozyton meter RS485 interface
ENERGY METER GAMA 300 LED BLINK INTERFACE
SCHMITT TRIGGER FOR METERS
