kwiecinski/BMS-and-offgrid-photovoltaic-management-system/hardware/PCB_and_schematic/Power tracking heater/power_tracking_heater.kicad_sch

## KiCad design hardware/PCB_and_schematic/Power tracking heater/power_tracking_heater.kicad_sch (2024-10-14)

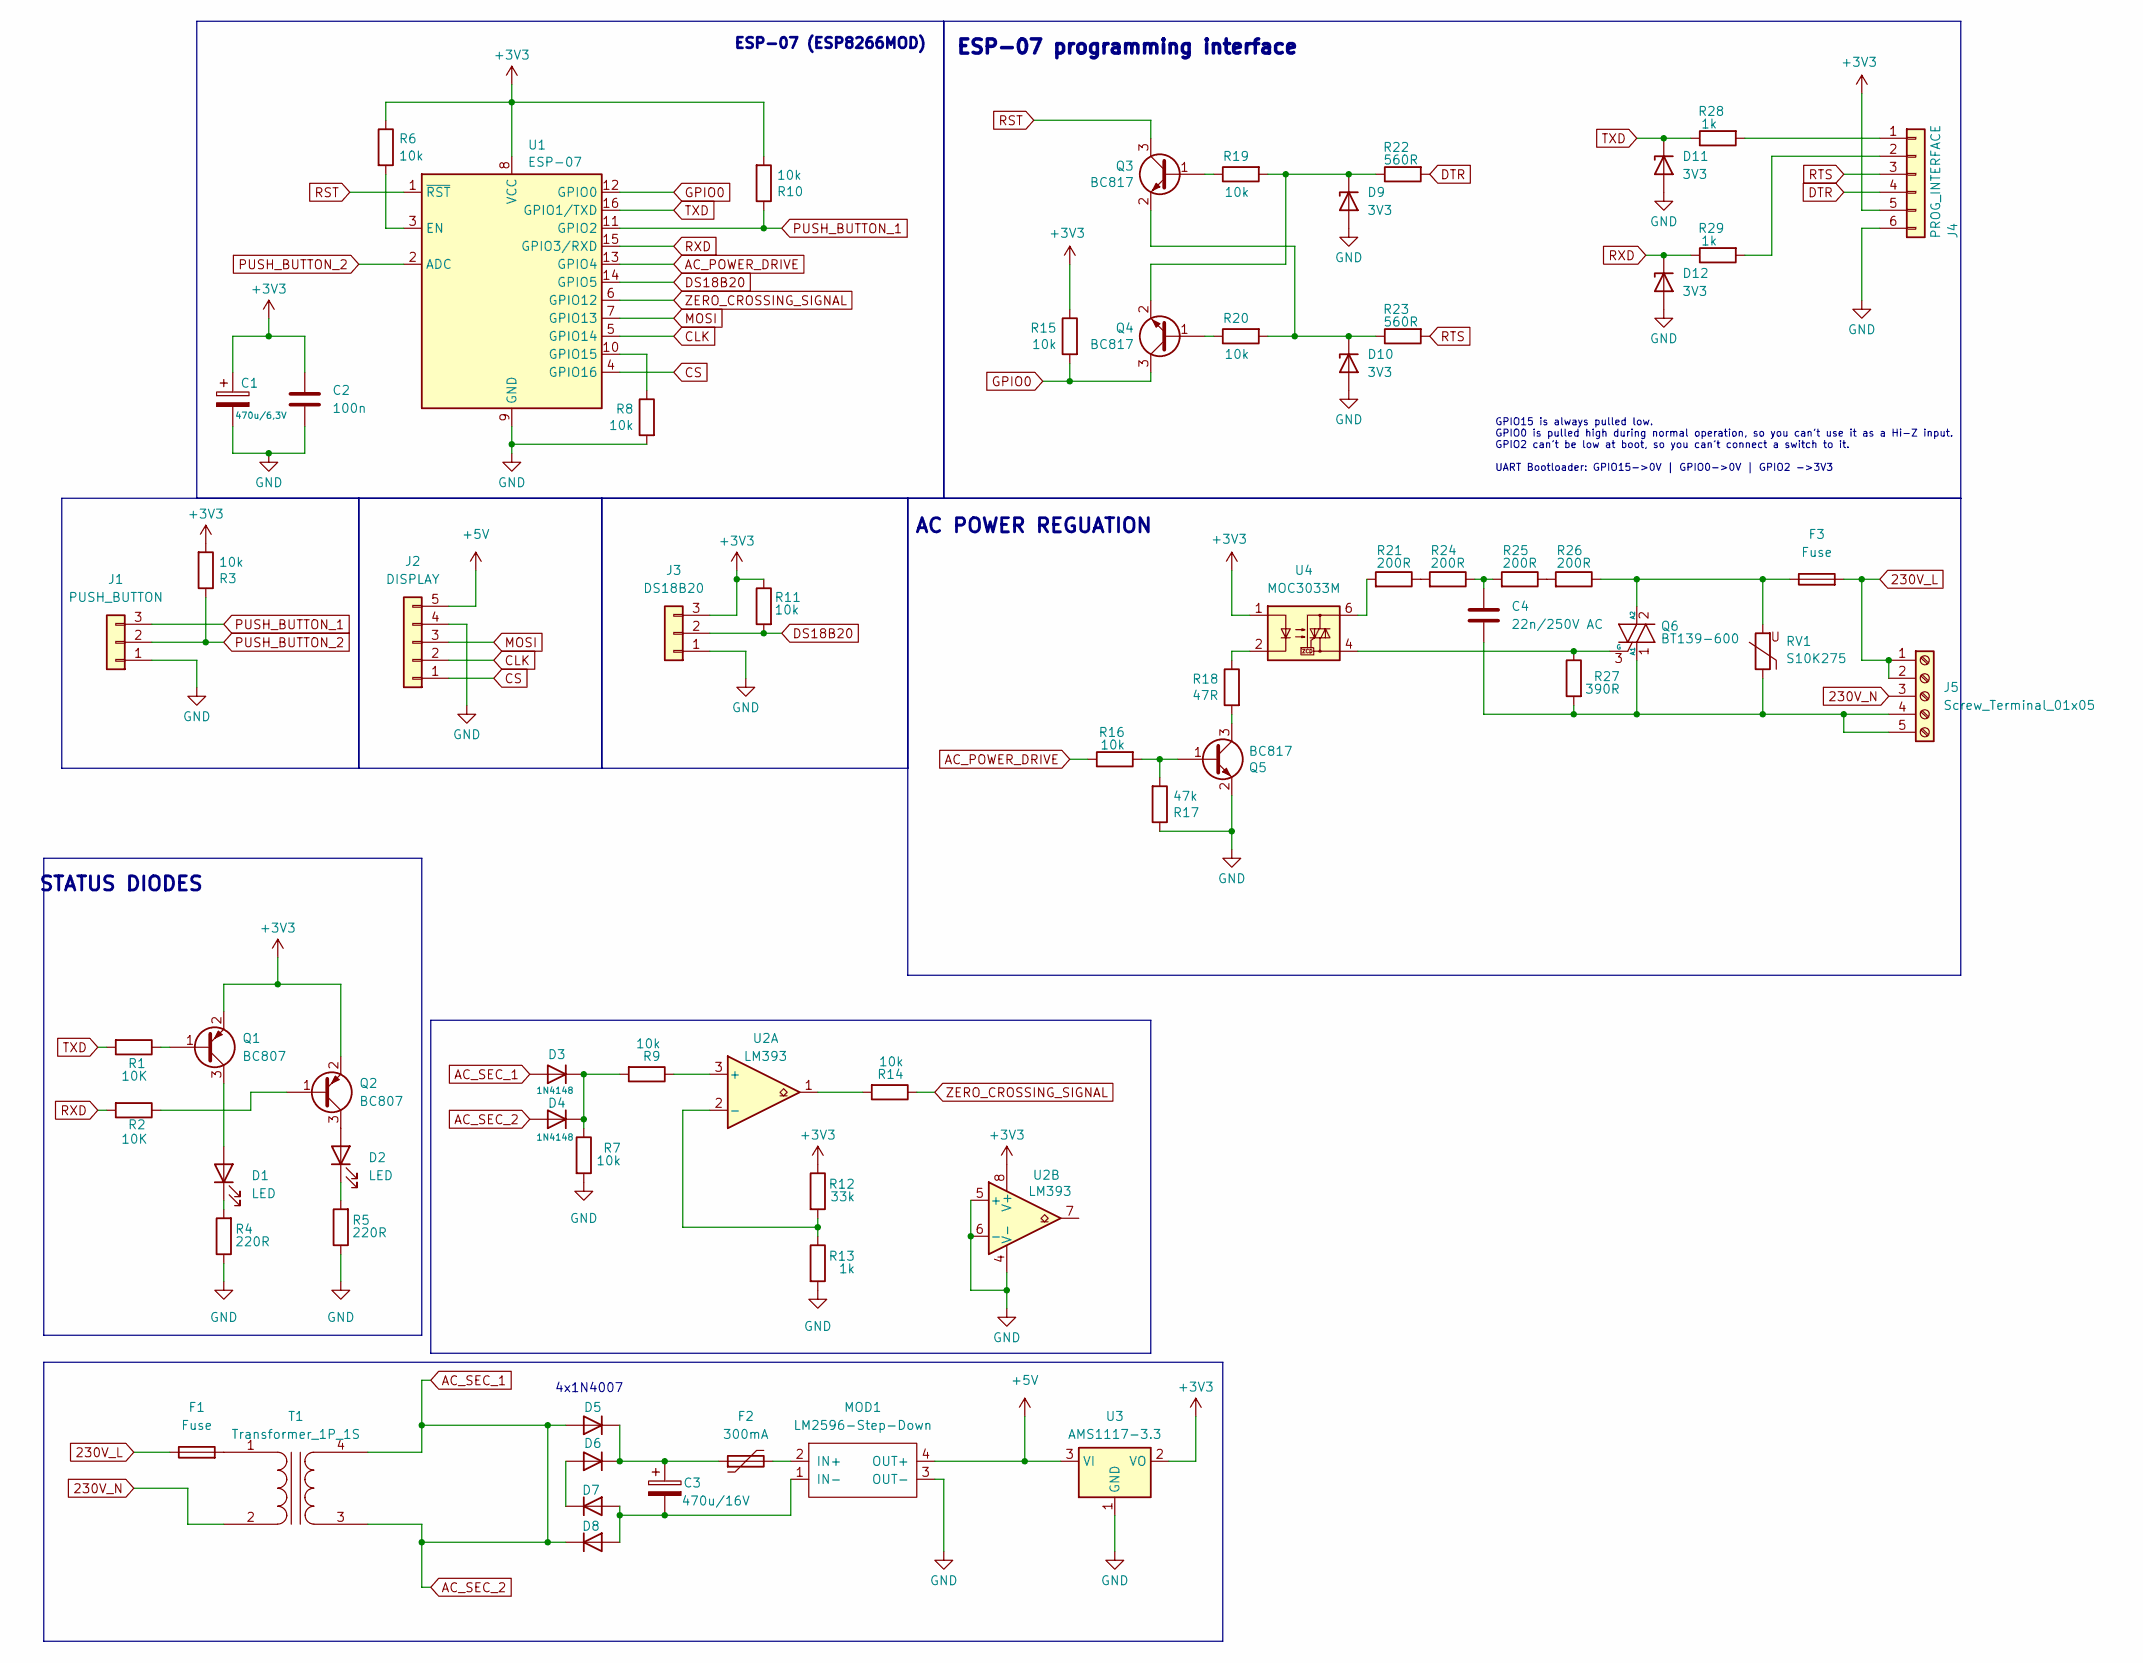
[picture p107: schematic power_tracking_heater.kicad_sch]

Parts:
C1: 470u/6,3V; CP_Elec_5x5.7
C2: 100n; C_0805_2012Metric
C3: 470u/16V; CP_Elec_5x5.7
C4: 22n/250V AC; C_Rect_L16.5mm_W6.0mm_P15.00mm_MKT
D1, D2: LED; LED_PLCC-2_3.4x3.0mm_KA
D3, D4: 1N4148; D_DO-35_SOD27_P7.62mm_Horizontal
D5, D6, D7, D8: 1N4007; DO-213AB_1-mediana
D9, D10, D11, D12: 3V3; D_MiniMELF
F1, F3: Fuse; Fuseholder_Clip-5x20mm_Eaton_1A5601-01_Inline_P20.80x6.76mm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
F2: 300mA; Fuse_2010_5025Metric
J1: PUSH_BUTTON; PinSocket_1x03_P2.54mm_Vertical
J2: DISPLAY; JST_XA_B05B-XASK-1_1x05_P2.50mm_Vertical
J3: DS18B20; JST_XA_B03B-XASK-1_1x03_P2.50mm_Vertical
J4: PROG_INTERFACE; Conn-01x06
J5: Screw_Terminal_01x05; Screw-Terminal-5.00mm-5pin
MOD1: LM2596-Step-Down; MP1504_Mini_3A_Step_Down_Conv
Q1, Q2: BC807; SOT-23
Q3, Q4, Q5: BC817; SOT-23
Q6: BT139-600; TO-220-3_V_Wide_Legs
R1, R2: 10K; R_0805_2012Metric_Pad1.20x1.40mm_HandSolder
R3, R7, R8, R9, R10, R11, R14, R15, R16, R19, R20: 10k; R_0805_2012Metric_Pad1.20x1.40mm_HandSolder
R4, R5: 220R; R_0805_2012Metric_Pad1.20x1.40mm_HandSolder
R6: 10k; C_0805_2012Metric
R12: 33k; R_0805_2012Metric_Pad1.20x1.40mm_HandSolder
R13, R28, R29: 1k; R_0805_2012Metric_Pad1.20x1.40mm_HandSolder
R17: 47k; R_0805_2012Metric_Pad1.20x1.40mm_HandSolder
R18: 47R; R_0805_2012Metric_Pad1.20x1.40mm_HandSolder
R21, R24, R25, R26: 200R; R_Axial_DIN0204_L3.6mm_D1.6mm_P7.62mm_Horizontal
R22, R23: 560R; R_0805_2012Metric_Pad1.20x1.40mm_HandSolder
R27: 390R; R_Axial_DIN0204_L3.6mm_D1.6mm_P5.08mm_Horizontal
RV1: S10K275; RV_Disc_D7mm_W3.5mm_P5mm
T1: Transformer_1P_1S; Transformer TS2-14
U1: ESP-07
U2: LM393; DIP-8_W7.62mm_LongPads
U3: AMS1117-3.3; SOT-223-3_TabPin2
U4: MOC3033M; DIP-6_W7.62mm_LongPads

Connections:
230V_L: F1.1, F3.2, J5.1, J5.2
230V_N: J5.3, T1.2 (AB)
+3V3: C1.1, C2.1, J3.3, J4.5, Q1.2 (E), Q2.2 (E), R3.2, R6.1, R10.2, R11.1, R12.1, R15.1, U1.8 (VCC), U2.8 (V+), U3.2 (VO), U4.1
+5V: J2.5, MOD1.4 (OUT+), U3.3 (VI)
AC_POWER_DRIVE: R16.1, U1.13 (GPIO4)
AC_SEC_1: D3.2 (A), D4.2 (A), D5.2 (A), D8.1 (K), T1.3 (SA), T1.4 (SB)
CLK: J2.2, U1.5 (GPIO14)
CS: J2.1, U1.4 (GPIO16)
DS18B20: J3.2, R11.2, U1.14 (GPIO5)
DTR: J4.4, R22.2
GND: C1.2, C2.2, D9.2 (A), D10.2 (A), D11.2 (A), D12.2 (A), J1.1, J2.4, J3.1, J4.6, MOD1.3 (OUT-), Q5.2 (E), R4.1, R5.1, R7.2, R8.2, R13.2, R17.1, U1.9 (GND), U2.4 (V-), U2.5 (+), U2.6 (-), U3.1 (GND)
GPIO0: Q4.3 (C), R15.2, U1.12 (GPIO0)
MOSI: J2.3, U1.7 (GPIO13)
unnamed: C3.1, D5.1 (K), D6.1 (K), F2.1
unnamed: C3.2, D7.2 (A), D8.2 (A), MOD1.1 (IN-)
unnamed: C4.1, R24.1, R25.2
unnamed: C4.2, J5.4, J5.5, Q6.1 (A1), R27.2, RV1.1
unnamed: D1.1 (K), R4.2
unnamed: D1.2 (A), Q1.3 (C)
unnamed: D2.1 (K), R5.2
unnamed: D2.2 (A), Q2.3 (C)
unnamed: D3.1 (K), D4.1 (K), R7.1, R9.2
unnamed: D6.2 (A), D7.1 (K)
unnamed: D9.1 (K), Q4.2 (E), R19.2, R22.1
unnamed: D10.1 (K), Q3.2 (E), R20.2, R23.1
unnamed: F1.2, T1.1 (AA)
unnamed: F2.2, MOD1.2 (IN+)
unnamed: F3.1, Q6.2 (A2), R26.1, RV1.2
unnamed: J4.1, R28.2
unnamed: J4.2, R29.2
unnamed: Q1.1 (B), R1.1
unnamed: Q2.1 (B), R2.1
unnamed: Q3.1 (B), R19.1
unnamed: Q4.1 (B), R20.1
unnamed: Q5.1 (B), R16.2, R17.2
unnamed: Q5.3 (C), R18.2
unnamed: Q6.3 (G), R27.1, U4.4
unnamed: R6.2, U1.3 (EN)
unnamed: R8.1, U1.10 (GPIO15)
unnamed: R9.1, U2.3 (+)
unnamed: R12.2, R13.1, U2.2 (-)
unnamed: R14.2, U2.1
unnamed: R18.1, U4.2
unnamed: R21.1, R24.2
unnamed: R21.2, U4.6
unnamed: R25.1, R26.2
PUSH_BUTTON_1: J1.3, R10.1, U1.11 (GPIO2)
PUSH_BUTTON_2: J1.2, R3.1, U1.2 (ADC)
RST: Q3.3 (C), U1.1 (~RST)
RTS: J4.3, R23.2
RXD: D12.1 (K), R2.2, R29.1, U1.15 (GPIO3/RXD)
TXD: D11.1 (K), R1.2, R28.1, U1.16 (GPIO1/TXD)
ZERO_CROSSING_SIGNAL: R14.1, U1.6 (GPIO12)

Notes on the sheet:
ESP-07 (ESP8266MOD)
STATUS DIODES
4x1N4007
GPIO15 is always pulled low. GPIO0 is pulled high during normal operation, so you can’t use it as a Hi-Z input. GPIO2 can’t be low at boot, so you can’t connect a switch to it. UART Bootloader: GPIO15->0V | GPIO0->0V | GPIO2 ->3V3
ESP-07 programming interface
AC POWER REGUATION
