kwiecinski/BMS-and-offgrid-photovoltaic-management-system/hardware/PCB_and_schematic/Misc_PCB/Misc_PCB/power_tracking_heater.kicad_sch

## KiCad design hardware/PCB_and_schematic/Misc_PCB/Misc_PCB/power_tracking_heater.kicad_sch (2024-10-14)

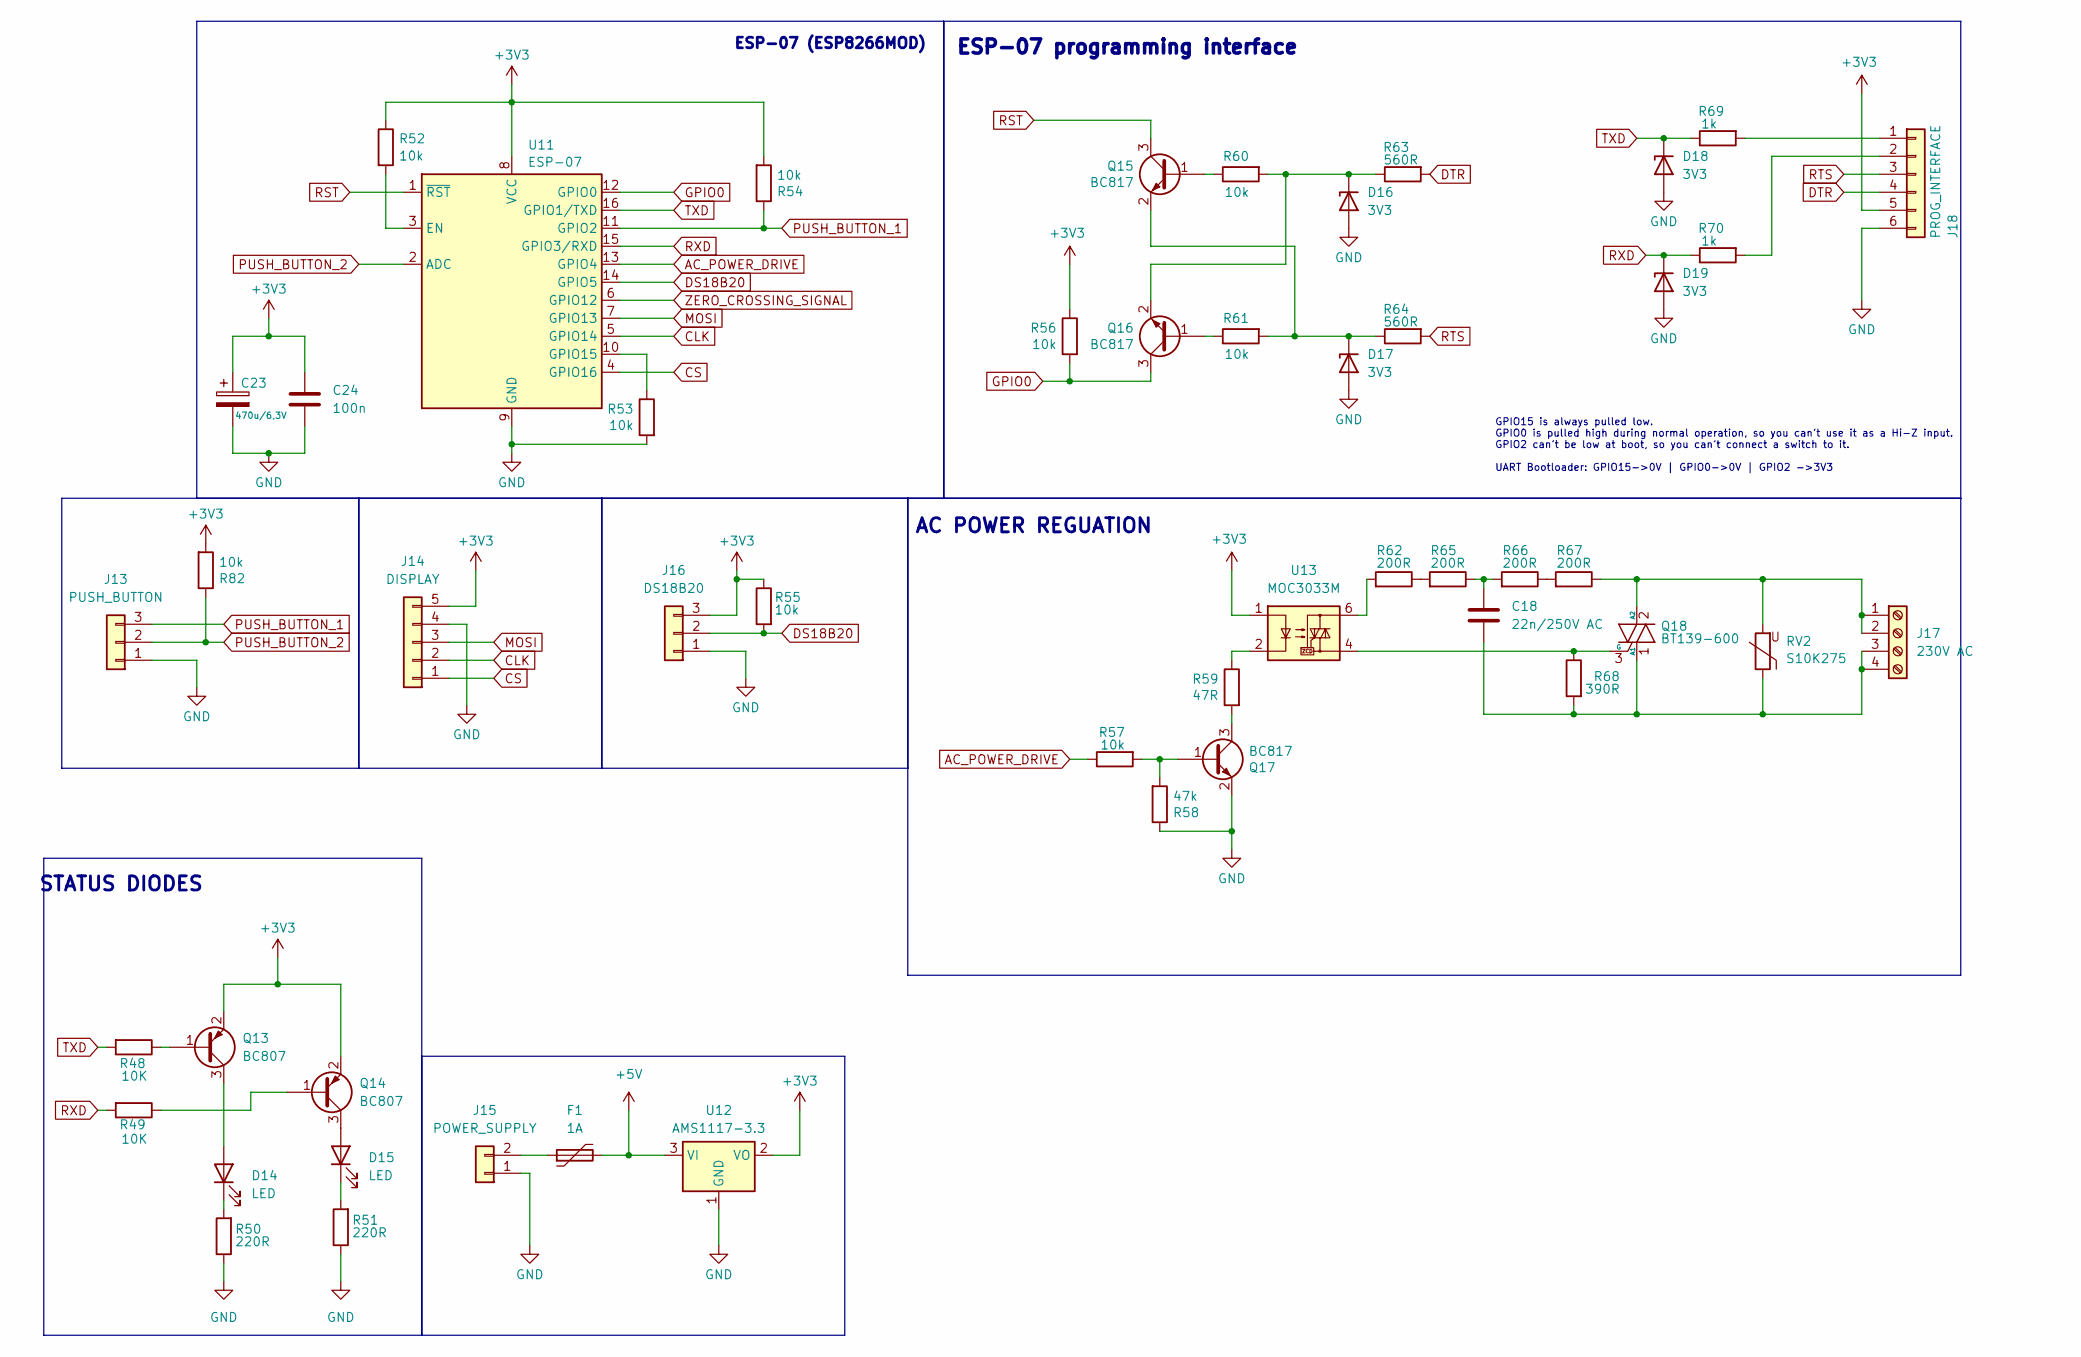
[picture p108: schematic power_tracking_heater.kicad_sch]

Parts:
C18: 22n/250V AC; C_Rect_L16.5mm_W6.0mm_P15.00mm_MKT
C23: 470u/6,3V; CP_Elec_5x5.7
C24: 100n; C_0805_2012Metric
D14, D15: LED; LED_PLCC-2_3.4x3.0mm_KA
D16, D17, D18, D19: 3V3; D_MiniMELF
F1: 1A; Fuse_2010_5025Metric
J13: PUSH_BUTTON; PinSocket_1x03_P2.54mm_Vertical
J14: DISPLAY; JST_XA_B05B-XASK-1_1x05_P2.50mm_Vertical
J15: POWER_SUPPLY; PinSocket_1x02_P2.54mm_Vertical
J16: DS18B20; JST_XA_B03B-XASK-1_1x03_P2.50mm_Vertical
J17: 230V AC; TerminalBlock_bornier-4_P5.08mm
J18: PROG_INTERFACE; Conn-01x06
Q13, Q14: BC807; SOT-23
Q15, Q16, Q17: BC817; SOT-23
Q18: BT139-600; TO-220-3_V_Wide_Legs
R48, R49: 10K; R_0805_2012Metric_Pad1.20x1.40mm_HandSolder
R50, R51: 220R; R_0805_2012Metric_Pad1.20x1.40mm_HandSolder
R52: 10k; C_0805_2012Metric
R53, R54, R55, R56, R57, R60, R61, R82: 10k; R_0805_2012Metric_Pad1.20x1.40mm_HandSolder
R58: 47k; R_0805_2012Metric_Pad1.20x1.40mm_HandSolder
R59: 47R; R_0805_2012Metric_Pad1.20x1.40mm_HandSolder
R62, R65, R66, R67: 200R; R_Axial_DIN0204_L3.6mm_D1.6mm_P7.62mm_Horizontal
R63, R64: 560R; R_0805_2012Metric_Pad1.20x1.40mm_HandSolder
R68: 390R; R_Axial_DIN0204_L3.6mm_D1.6mm_P7.62mm_Horizontal
R69, R70: 1k; R_0805_2012Metric_Pad1.20x1.40mm_HandSolder
RV2: S10K275; RV_Disc_D7mm_W3.5mm_P5mm
U11: ESP-07
U12: AMS1117-3.3; SOT-223-3_TabPin2
U13: MOC3033M; DIP-6_W7.62mm_LongPads

Connections:
+3V3: C23.1, C24.1, J14.5, J16.3, J18.5, Q13.2 (E), Q14.2 (E), R52.1, R54.2, R55.1, R56.1, R82.2, U11.8 (VCC), U12.2 (VO), U13.1
+5V: F1.2, U12.3 (VI)
AC_POWER_DRIVE: R57.1, U11.13 (GPIO4)
CLK: J14.2, U11.5 (GPIO14)
CS: J14.1, U11.4 (GPIO16)
DS18B20: J16.2, R55.2, U11.14 (GPIO5)
DTR: J18.4, R63.2
GND: C23.2, C24.2, D16.2 (A), D17.2 (A), D18.2 (A), D19.2 (A), J13.1, J14.4, J15.1, J16.1, J18.6, Q17.2 (E), R50.1, R51.1, R53.2, R58.1, U11.9 (GND), U12.1 (GND)
GPIO0: Q16.3 (C), R56.2, U11.12 (GPIO0)
MOSI: J14.3, U11.7 (GPIO13)
unnamed: C18.1, R65.1, R66.2
unnamed: C18.2, J17.3, J17.4, Q18.1 (A1), R68.2, RV2.1
unnamed: D14.1 (K), R50.2
unnamed: D14.2 (A), Q13.3 (C)
unnamed: D15.1 (K), R51.2
unnamed: D15.2 (A), Q14.3 (C)
unnamed: D16.1 (K), Q16.2 (E), R60.2, R63.1
unnamed: D17.1 (K), Q15.2 (E), R61.2, R64.1
unnamed: F1.1, J15.2
unnamed: J17.1, J17.2, Q18.2 (A2), R67.1, RV2.2
unnamed: J18.1, R69.2
unnamed: J18.2, R70.2
unnamed: Q13.1 (B), R48.1
unnamed: Q14.1 (B), R49.1
unnamed: Q15.1 (B), R60.1
unnamed: Q16.1 (B), R61.1
unnamed: Q17.1 (B), R57.2, R58.2
unnamed: Q17.3 (C), R59.2
unnamed: Q18.3 (G), R68.1, U13.4
unnamed: R52.2, U11.3 (EN)
unnamed: R53.1, U11.10 (GPIO15)
unnamed: R59.1, U13.2
unnamed: R62.1, R65.2
unnamed: R62.2, U13.6
unnamed: R66.1, R67.2
PUSH_BUTTON_1: J13.3, R54.1, U11.11 (GPIO2)
PUSH_BUTTON_2: J13.2, R82.1, U11.2 (ADC)
RST: Q15.3 (C), U11.1 (~RST)
RTS: J18.3, R64.2
RXD: D19.1 (K), R49.2, R70.1, U11.15 (GPIO3/RXD)
TXD: D18.1 (K), R48.2, R69.1, U11.16 (GPIO1/TXD)
ZERO_CROSSING_SIGNAL: U11.6 (GPIO12)

Notes on the sheet:
ESP-07 (ESP8266MOD)
STATUS DIODES
GPIO15 is always pulled low. GPIO0 is pulled high during normal operation, so you can’t use it as a Hi-Z input. GPIO2 can’t be low at boot, so you can’t connect a switch to it. UART Bootloader: GPIO15->0V | GPIO0->0V | GPIO2 ->3V3
ESP-07 programming interface
AC POWER REGUATION
