kwiecinski/BMS-and-offgrid-photovoltaic-management-system/hardware/PCB_and_schematic/Power_and_signal_splitter/splitter/router_camera_power_supply.kicad_sch

## KiCad design hardware/PCB_and_schematic/Power_and_signal_splitter/splitter/router_camera_power_supply.kicad_sch (2024-09-16)

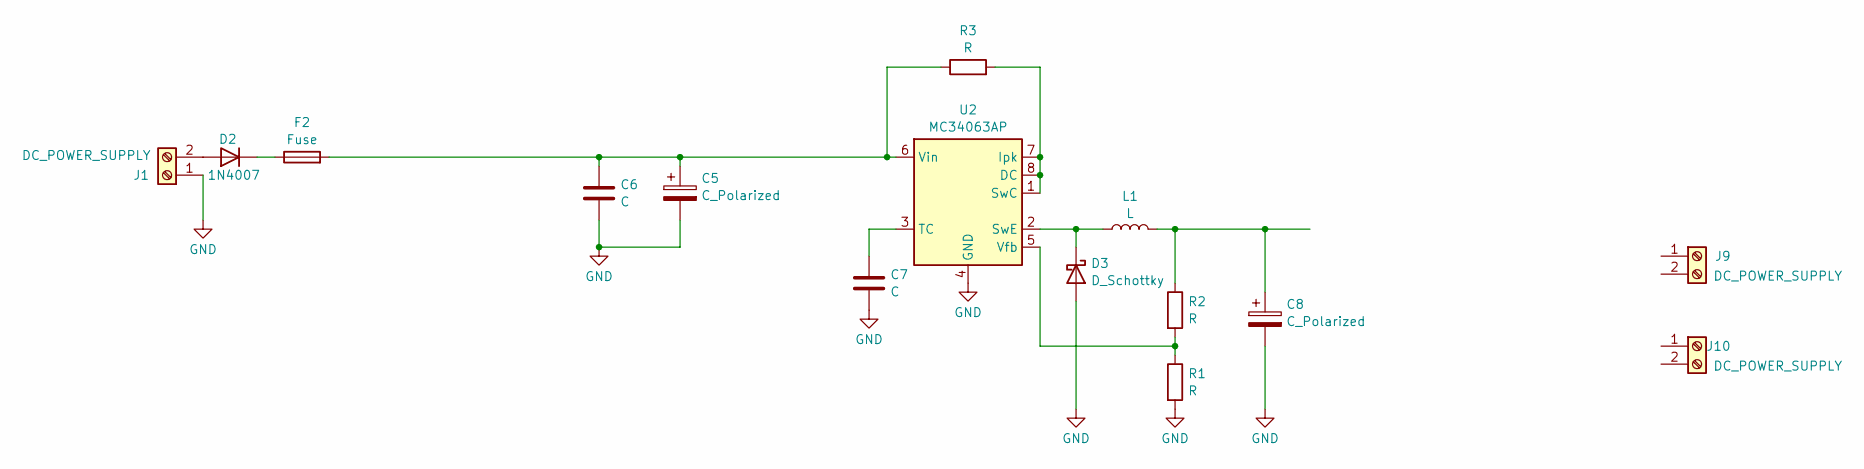
[picture p109: schematic router_camera_power_supply.kicad_sch]

Parts:
C5, C8: C_Polarized
C6, C7: C
D2: 1N4007; D_DO-41_SOD81_P10.16mm_Horizontal
D3: D_Schottky
F2: Fuse; Fuseholder_Clip-5x20mm_Eaton_1A5601-01_Inline_P20.80x6.76mm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
J1, J9, J10: DC_POWER_SUPPLY; TerminalBlock_Altech_AK300-2_P5.00mm
L1: L
R1, R2, R3: R
U2: MC34063AP; DIP-8_W7.62mm

Connections:
GND: C5.2, C6.2, C7.2, C8.2, D3.2 (A), J1.1, R1.2, U2.4 (GND)
unnamed: C5.1, C6.1, F2.2, R3.1, U2.6 (Vin)
unnamed: C7.1, U2.3 (TC)
unnamed: C8.1, L1.2, R2.1
unnamed: D2.1 (K), F2.1
unnamed: D2.2 (A), J1.2
unnamed: D3.1 (K), L1.1, U2.2 (SwE)
unnamed: R1.1, R2.2, U2.5 (Vfb)
unnamed: R3.2, U2.1 (SwC), U2.7 (Ipk), U2.8 (DC)
