kwiecinski/BMS-and-offgrid-photovoltaic-management-system/software/Balancer-AVR.X/current_limiter.h

/* 
 * File:   current_limiter.h
 * Author: RaD
 *
 * Created on May 15, 2025, 12:32 PM
 */

#ifndef CURRENT_LIMITER_H
#define	CURRENT_LIMITER_H

#ifdef	__cplusplus
extern "C" {
#endif


void current_limiter(void);

#ifdef	__cplusplus
}
#endif

#endif	/* CURRENT_LIMITER_H */
