kwiecinski/BMS-and-offgrid-photovoltaic-management-system/software/Balancer-AVR.X/modbus_rtu.h

/* 
 * File:   modbus_rtu.h
 * Author: LPC-user
 *
 * Created on 27 maja 2025, 09:41
 */

#ifndef MODBUS_RTU_H
#define	MODBUS_RTU_H

#ifdef	__cplusplus
extern "C" {
#endif




#ifdef	__cplusplus
}
#endif

#endif	/* MODBUS_RTU_H */
