kwiecinski/BMS-and-offgrid-photovoltaic-management-system/software/Balancer-AVR.X/debug.h

/* 
 * File:   debug.h
 * Author: LPC-user
 *
 * Created on 23 maja 2025, 11:44
 */

#ifndef DEBUG_H
#define	DEBUG_H

#ifdef	__cplusplus
extern "C" {
#endif

void printf_debug(balancer_struct *ptr, PID *pid);



#ifdef	__cplusplus
}
#endif

#endif	/* DEBUG_H */
