kwiecinski/BMS-and-offgrid-photovoltaic-management-system/software/Balancer-AVR.X/inits.h

/* 
 * File:   inits.h
 * Author: RaD
 *
 * Created on May 8, 2025, 3:46 PM
 */

#ifndef INITS_H
#define	INITS_H

#ifdef	__cplusplus
extern "C" {
#endif


void initialize(void);

    
    
    
#ifdef	__cplusplus
}
#endif

#endif	/* INITS_H */
