kwiecinski/BMS-and-offgrid-photovoltaic-management-system/software/Balancer-AVR.X/interrupts.h

/* 
 * File:   interrupts.h
 * Author: User
 *
 * Created on 16 maja 2025, 22:27
 */

#ifndef INTERRUPTS_H
#define	INTERRUPTS_H

#ifdef	__cplusplus
extern "C" {
#endif


void tcb0_handler(void);
uint32_t millis(void);

#ifdef	__cplusplus
}
#endif

#endif	/* INTERRUPTS_H */
