kwiecinski/BMS-and-offgrid-photovoltaic-management-system/software/Balancer.X/adc.h

#ifndef XC_HEADER_TEMPLATE_H
#define	XC_HEADER_TEMPLATE_H

#include <xc.h>


void ADC_Init(void);
unsigned int ADC_Read_ADC_Result(void);
unsigned int read_voltage(void) ;

#endif	/* XC_HEADER_TEMPLATE_H */
