kwiecinski/BMS-and-offgrid-photovoltaic-management-system/software/Balancer.X/sw_uart.h

///////////////////////////////////////////////////////////////////////////////
//
//
//
//
///////////////////////////////////////////////////////////////////////////////

#ifndef SW_UART
#define SW_UART


void SendUART_debug(unsigned char data);

//void SendArrayUART_debug(unsigned char *data, unsigned char size);
//void SendDigitUART_debug(unsigned int data);
//void SendInt32ToUART(int32_t value);
#endif
